gmofishsauce/yarc/img/2022-04-03/Clock and Downloader Extension Sketch.png

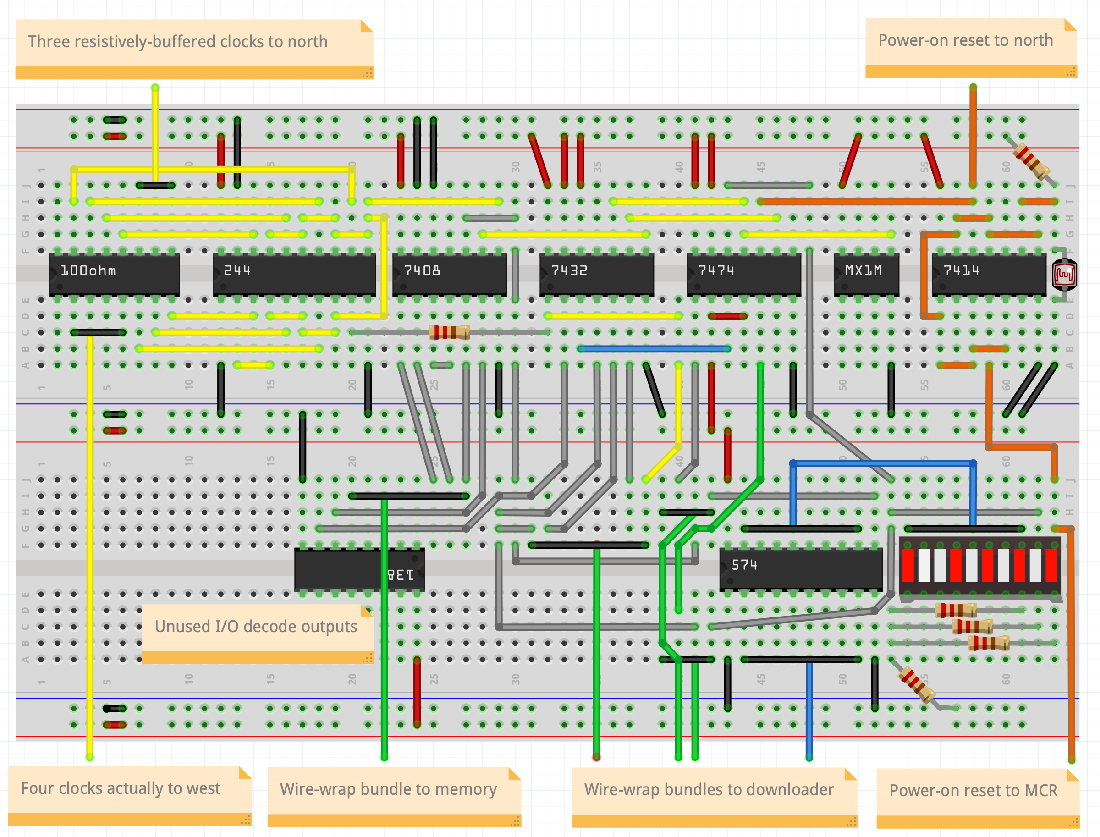
img/2022-04-03/Clock and Downloader Extension Sketch.png
