gmofishsauce/yarc/img/2022-04-03/Downloader Sketch.png

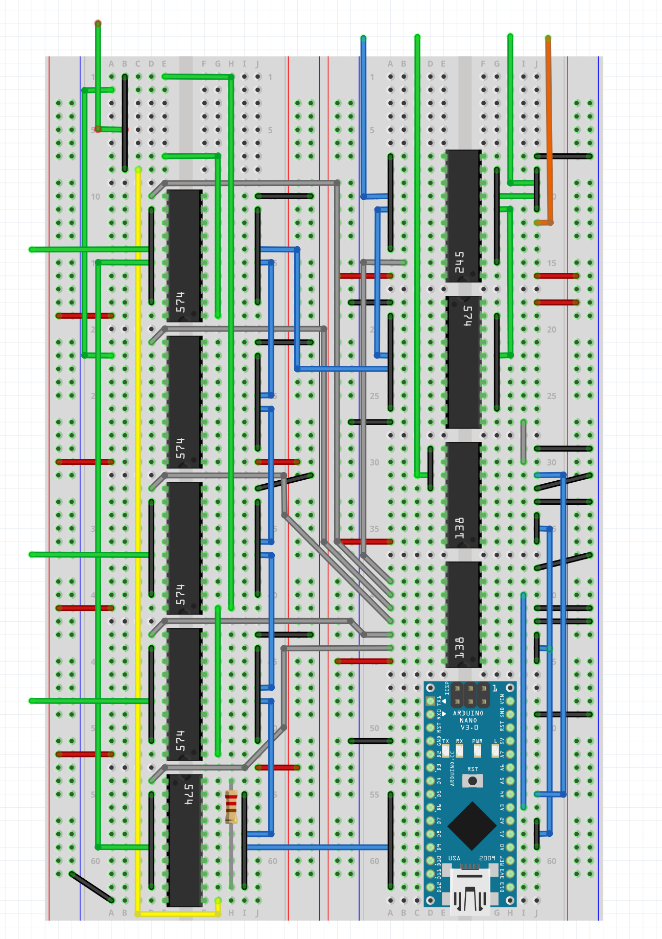
img/2022-04-03/Downloader Sketch.png
