gmofishsauce/yarc/img/2022-04-03/Memory Sketch (no busses).png

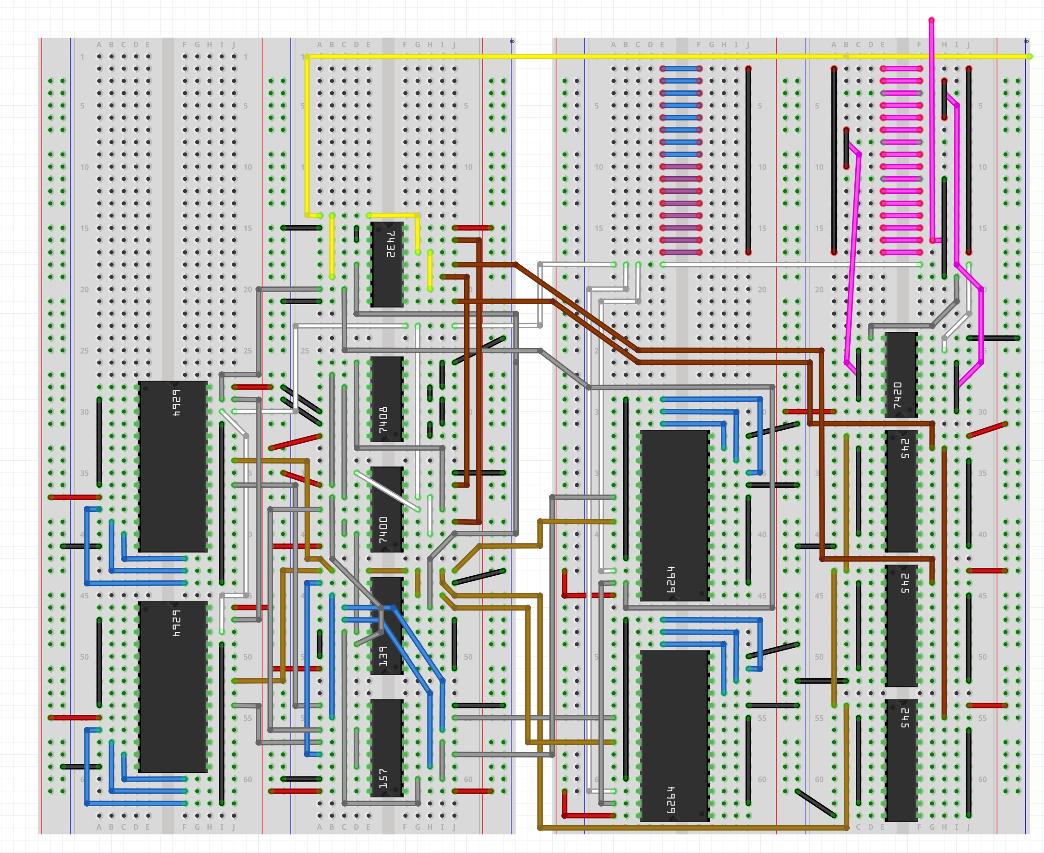
img/2022-04-03/Memory Sketch (no busses).png
