gmofishsauce/yarc/img/2022-07-07/clock_downloader_extension_fritzing.png

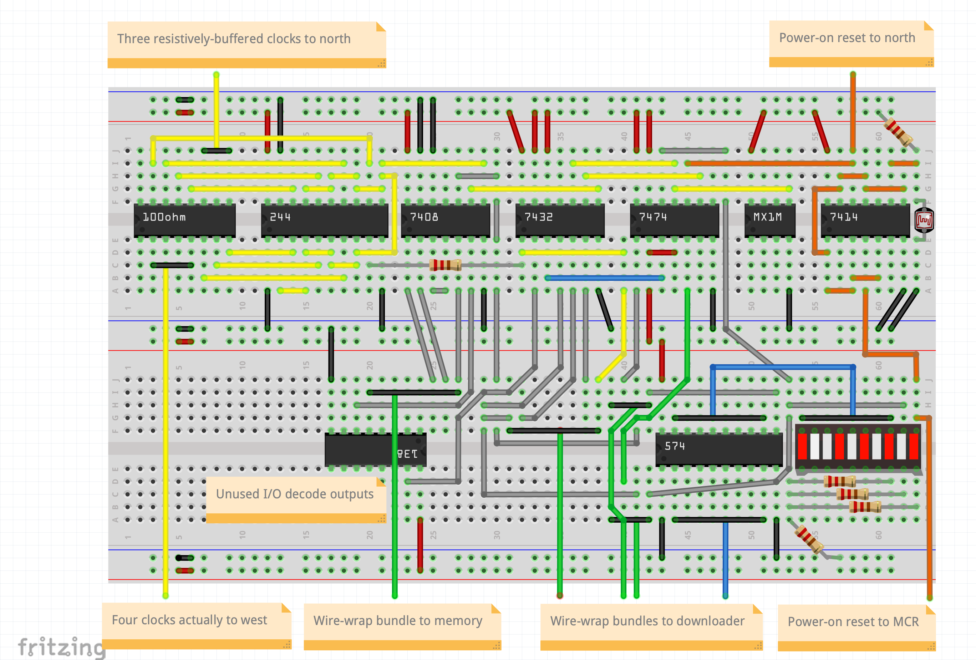
img/2022-07-07/clock_downloader_extension_fritzing.png
