gmofishsauce/yarc/img/2022-07-07/downloader_core_kicad.png

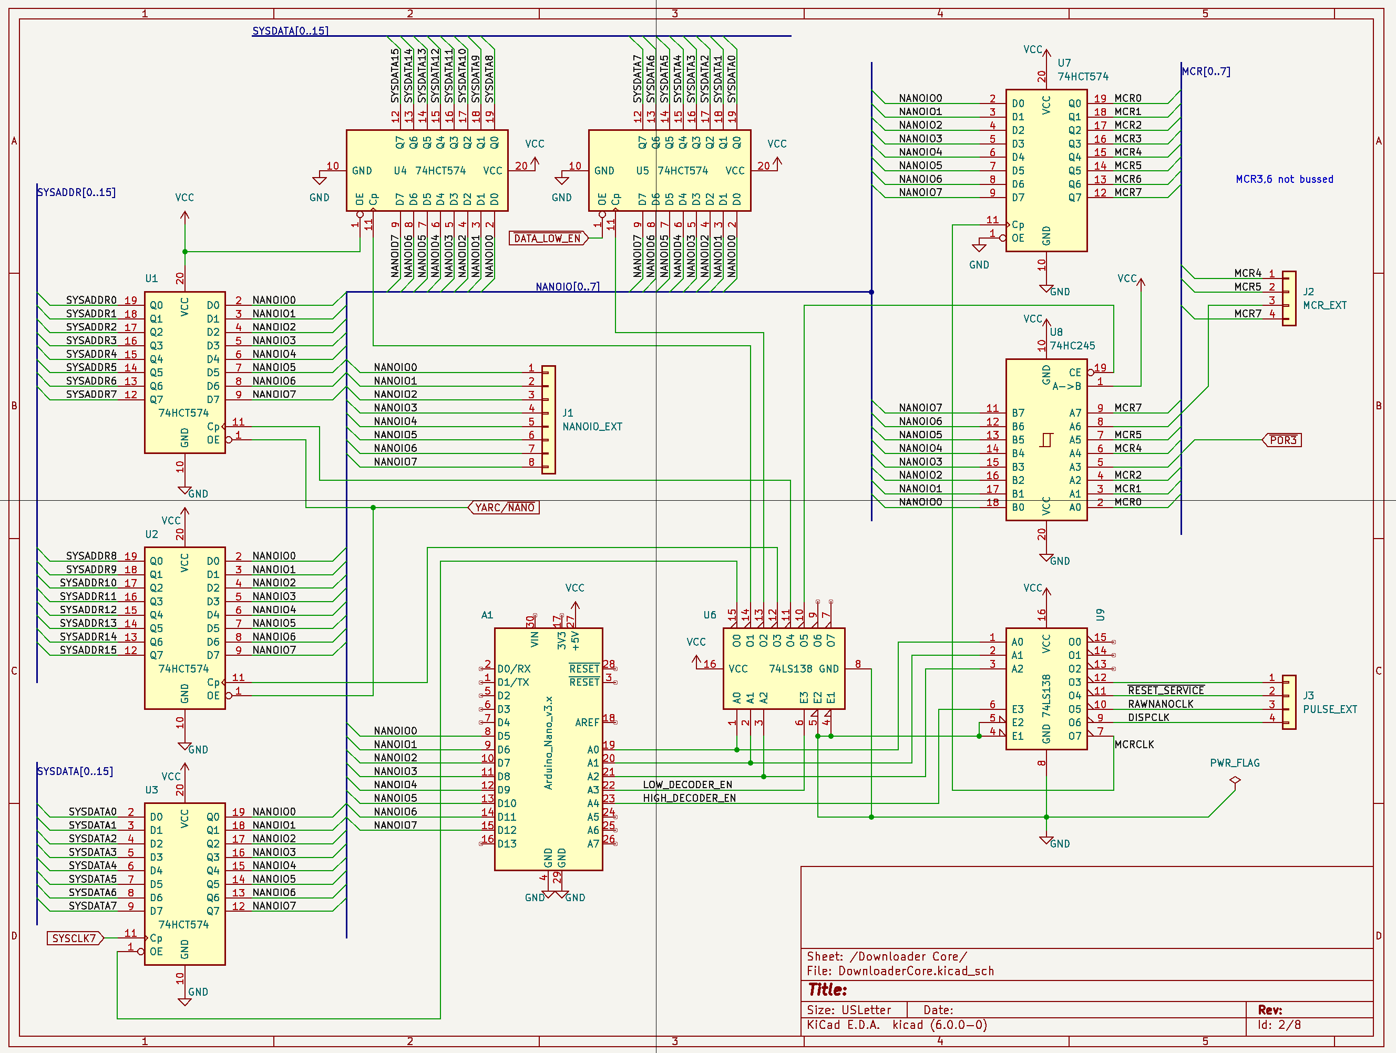
img/2022-07-07/downloader_core_kicad.png
