gmofishsauce/yarc/img/2022-07-07/downloader_fritzing.png

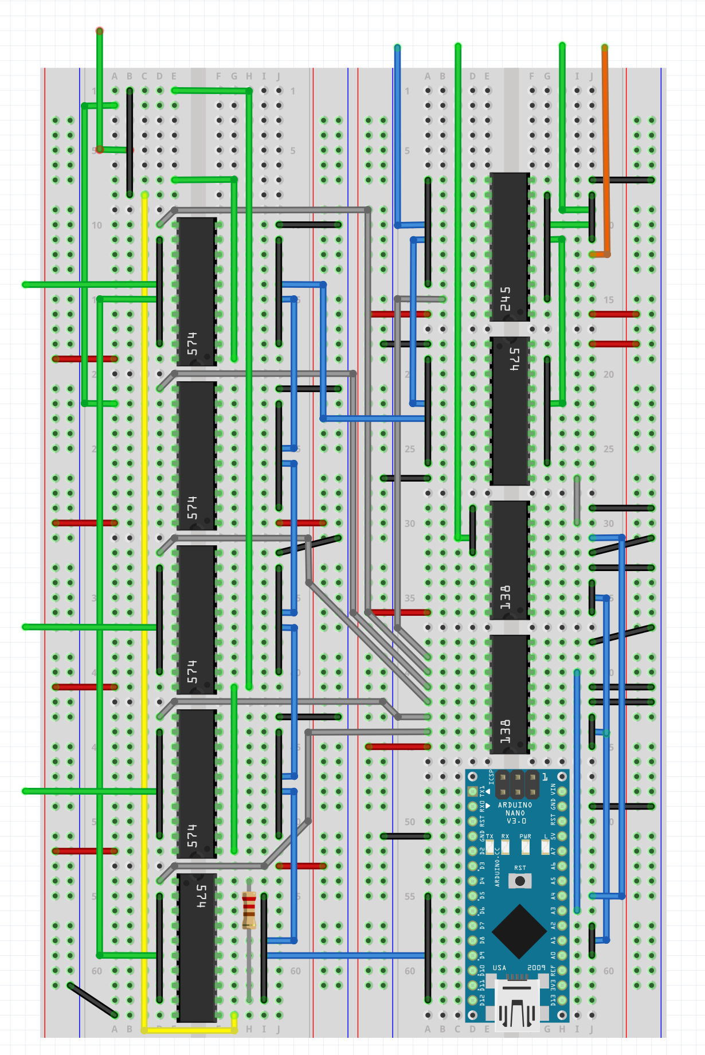
img/2022-07-07/downloader_fritzing.png
