gmofishsauce/yarc/img/2022-07-07/mem_pic_2.jpeg

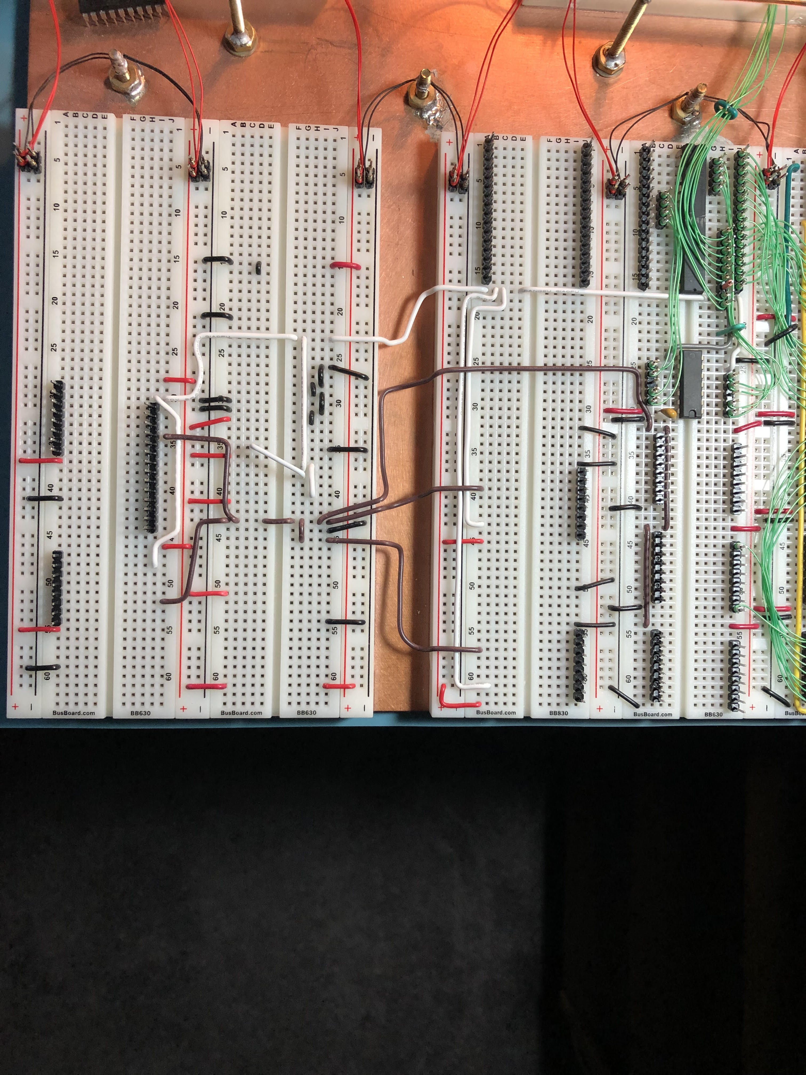
img/2022-07-07/mem_pic_2.jpeg
