gmofishsauce/yarc/img/2022-07-07/mem_pic_3.jpeg

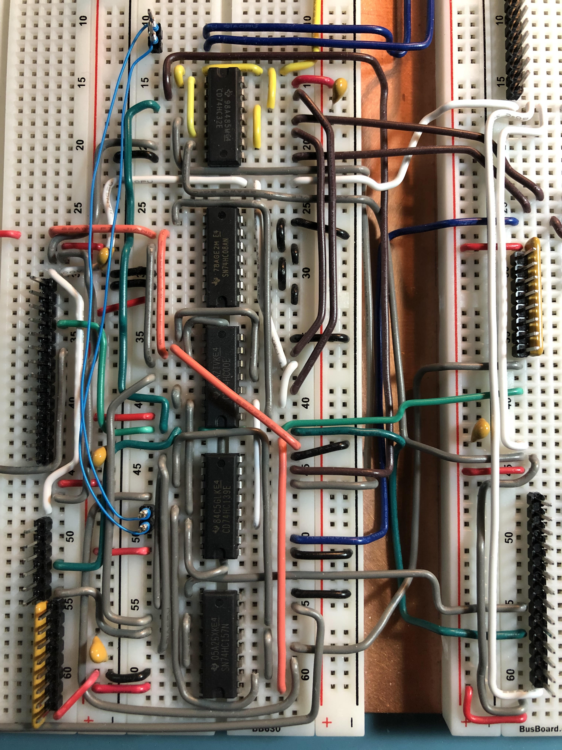
img/2022-07-07/mem_pic_3.jpeg
