gmofishsauce/yarc/img/2022-07-07/mem_pic_5.jpeg

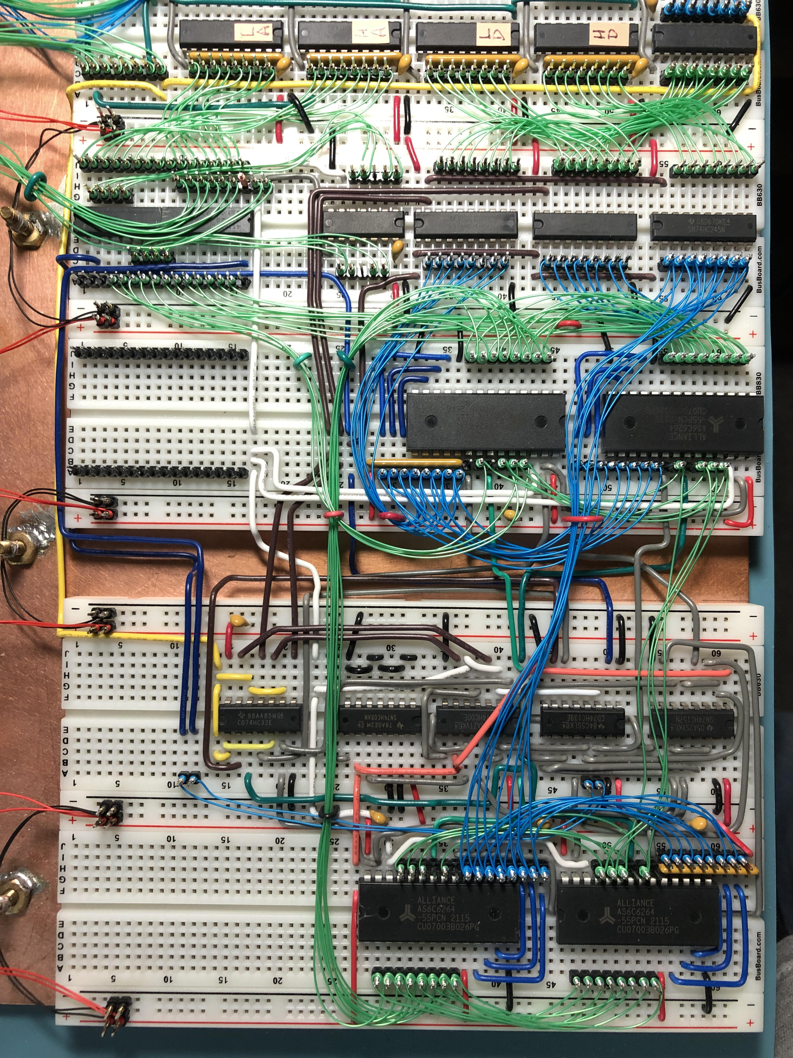
img/2022-07-07/mem_pic_5.jpeg
