gmofishsauce/yarc/img/2022-07-07/memory_fritzing.png

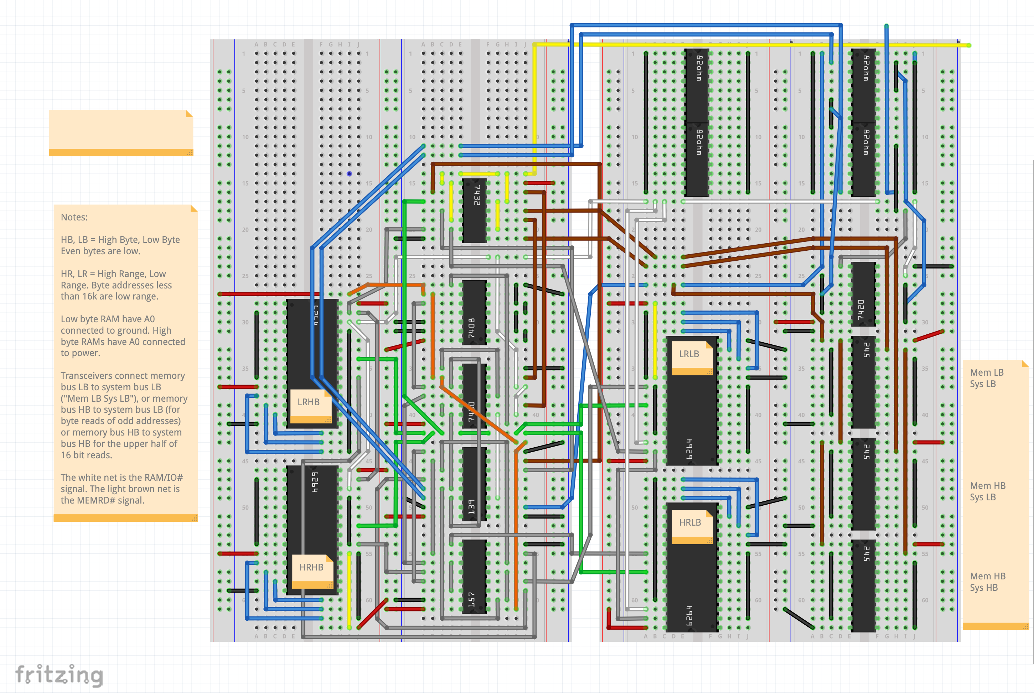
img/2022-07-07/memory_fritzing.png
