gmofishsauce/yarc/img/2022-07-07/memory_kicad.png

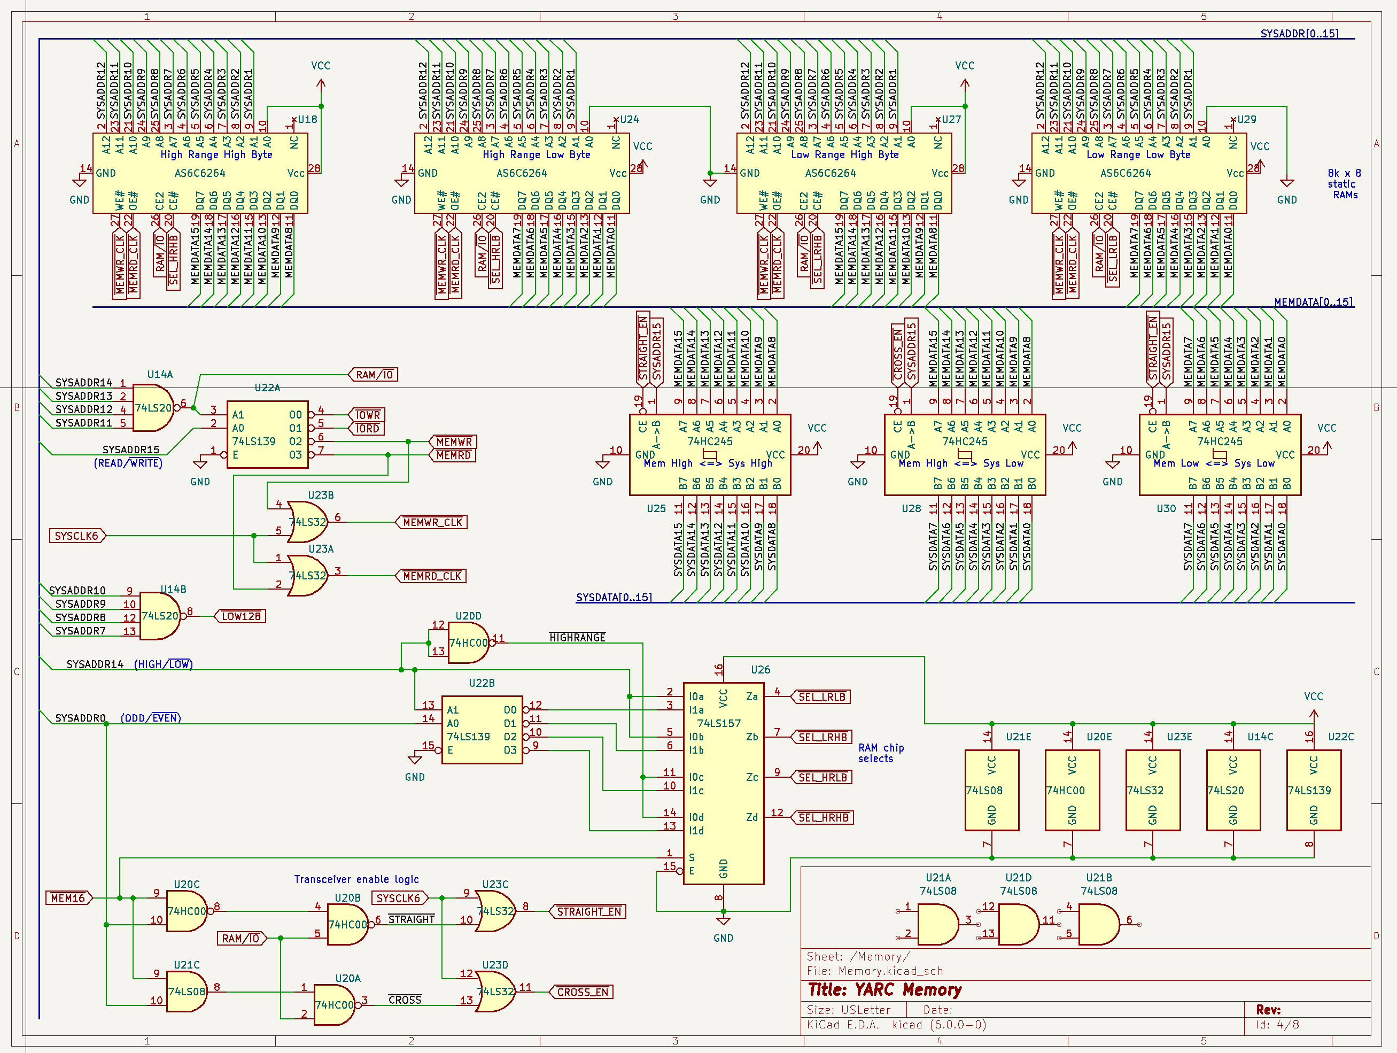
img/2022-07-07/memory_kicad.png
