gmofishsauce/yarc/img/2022-07-07/microcode_control_kicad.png

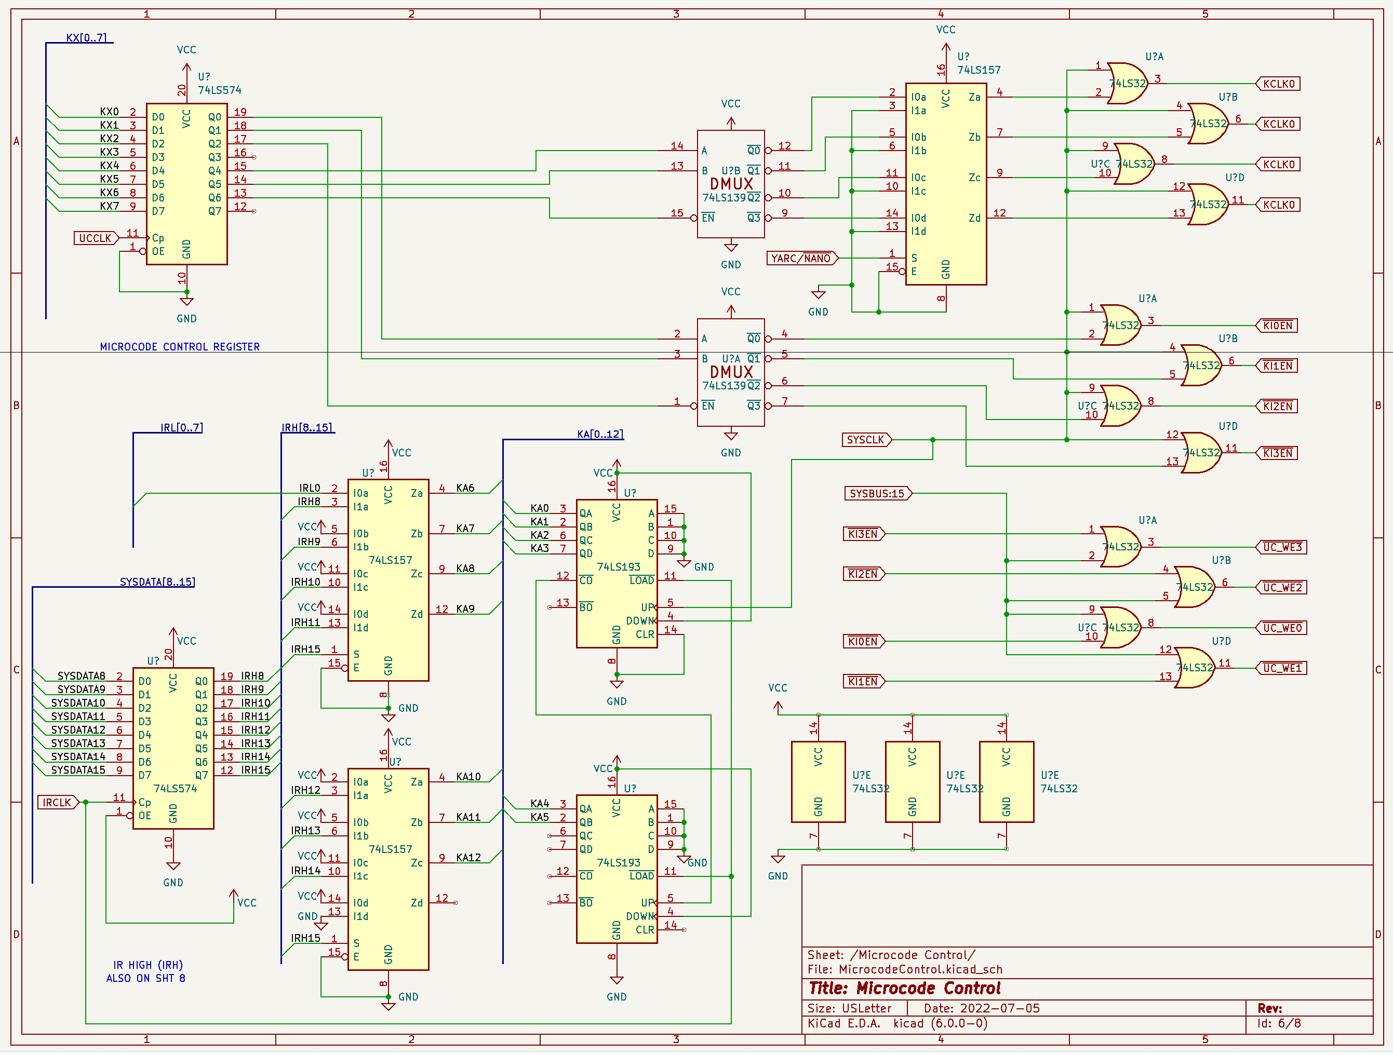
img/2022-07-07/microcode_control_kicad.png
