gmofishsauce/yarc/img/2022-07-07/microcode_fritzing.png

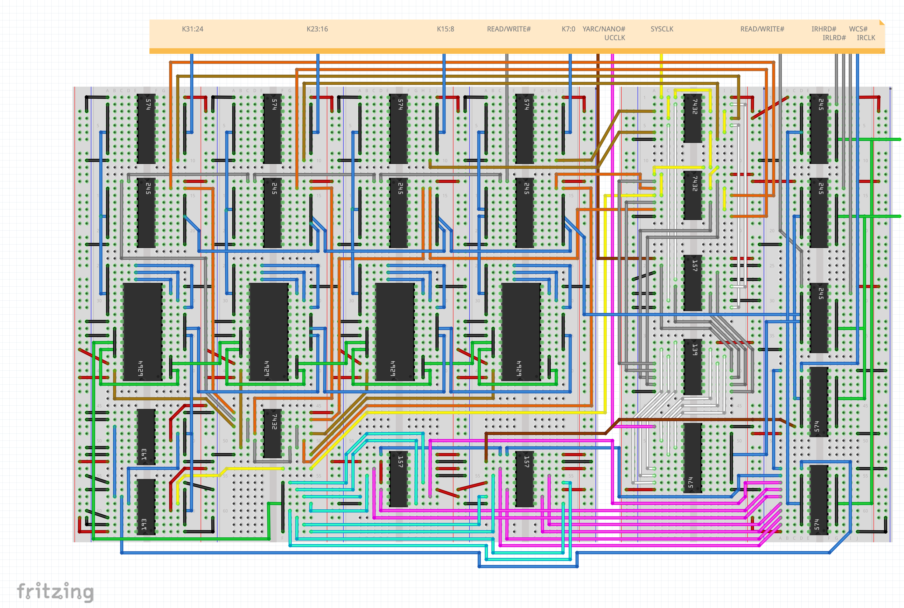
img/2022-07-07/microcode_fritzing.png
