gmofishsauce/yarc/img/2022-07-07/microcode_transceivers_kicad.png

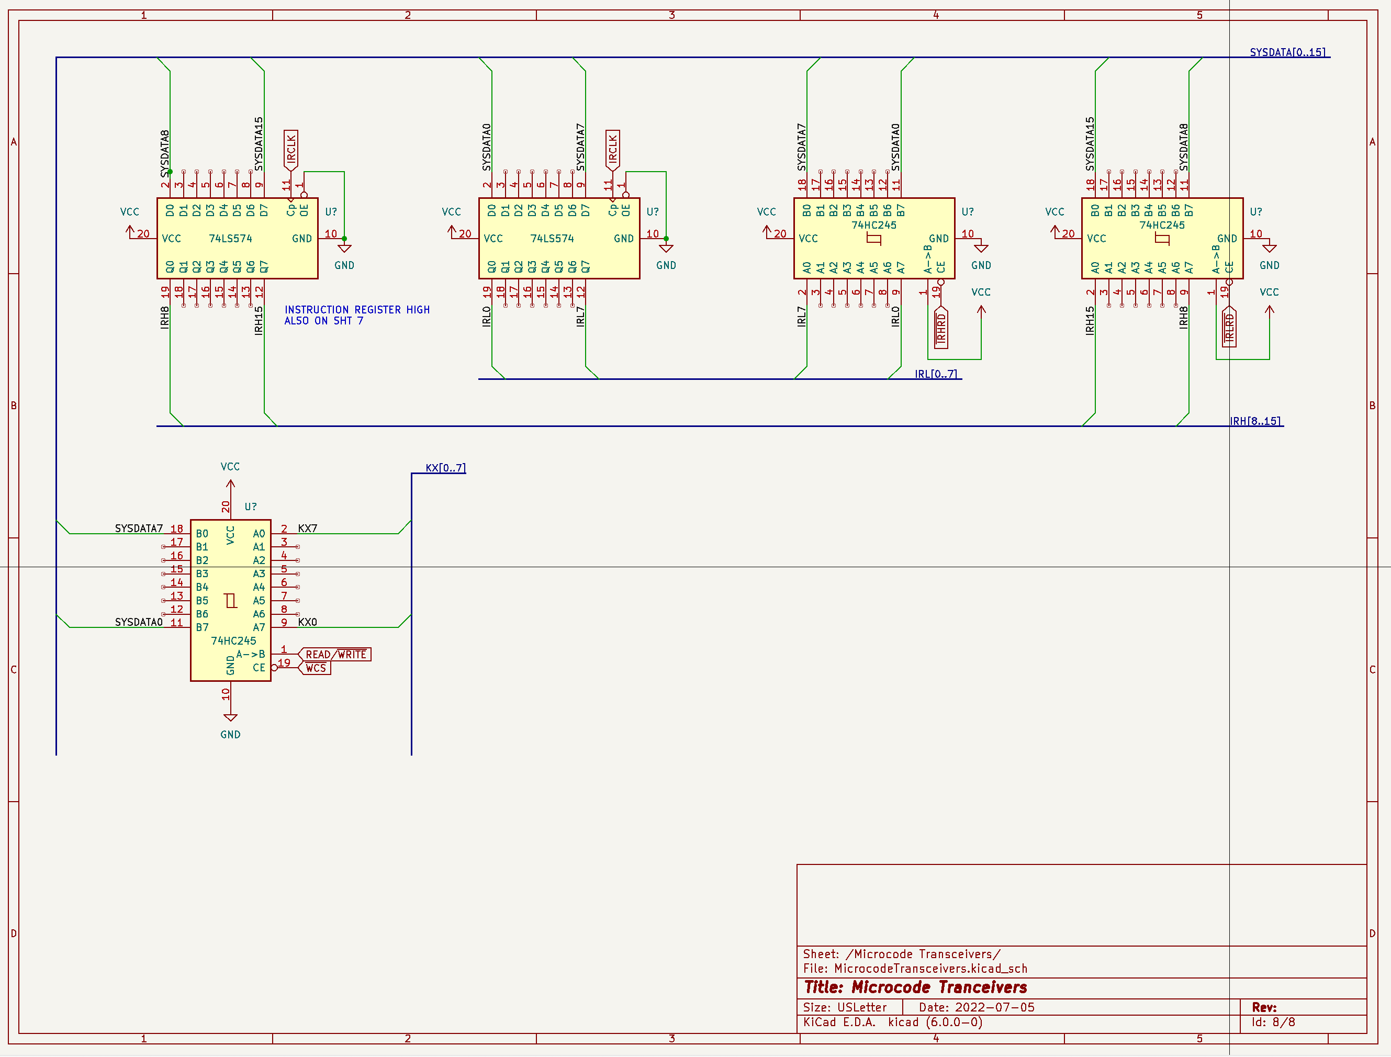
img/2022-07-07/microcode_transceivers_kicad.png
