gmofishsauce/yarc/img/2022-07-07/microode_engine_kicad.png

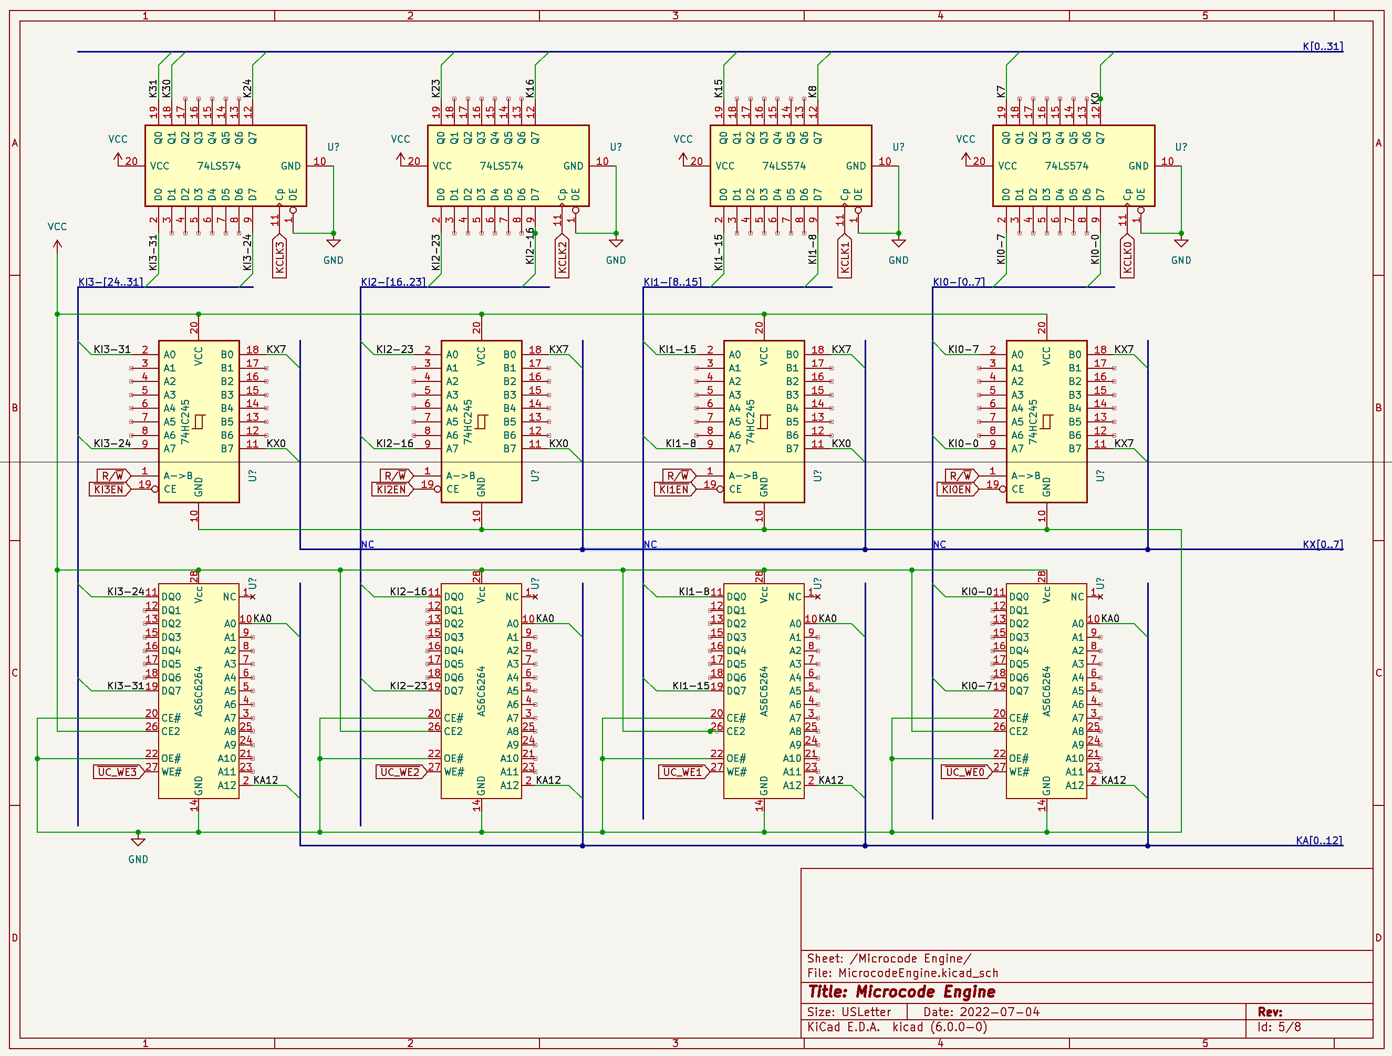
img/2022-07-07/microode_engine_kicad.png
