gmofishsauce/yarc/img/2022-07-07/Packaging-1.jpg

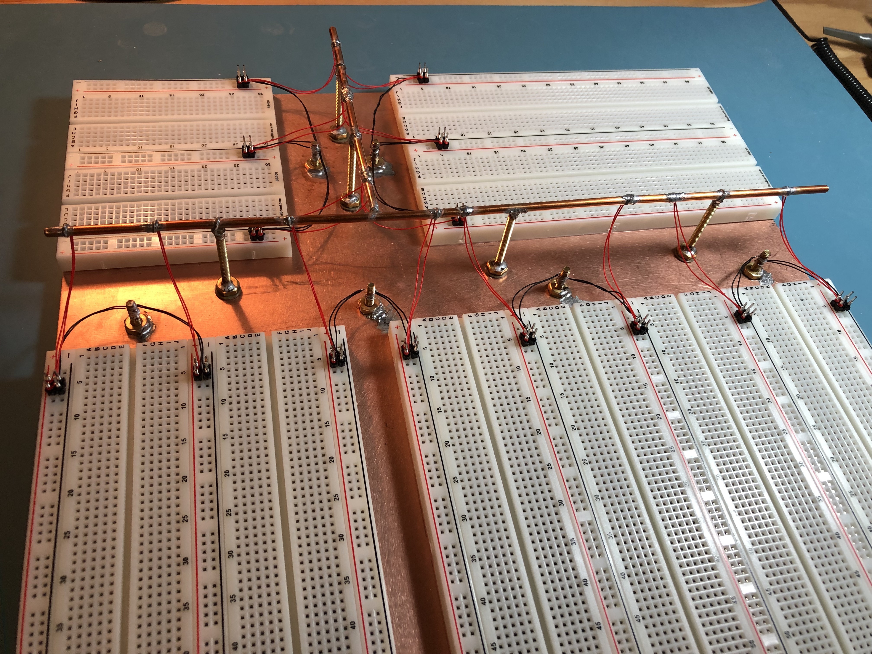
img/2022-07-07/Packaging-1.jpg
