gmofishsauce/yarc/img/2022-07-07/Packaging-2.jpg

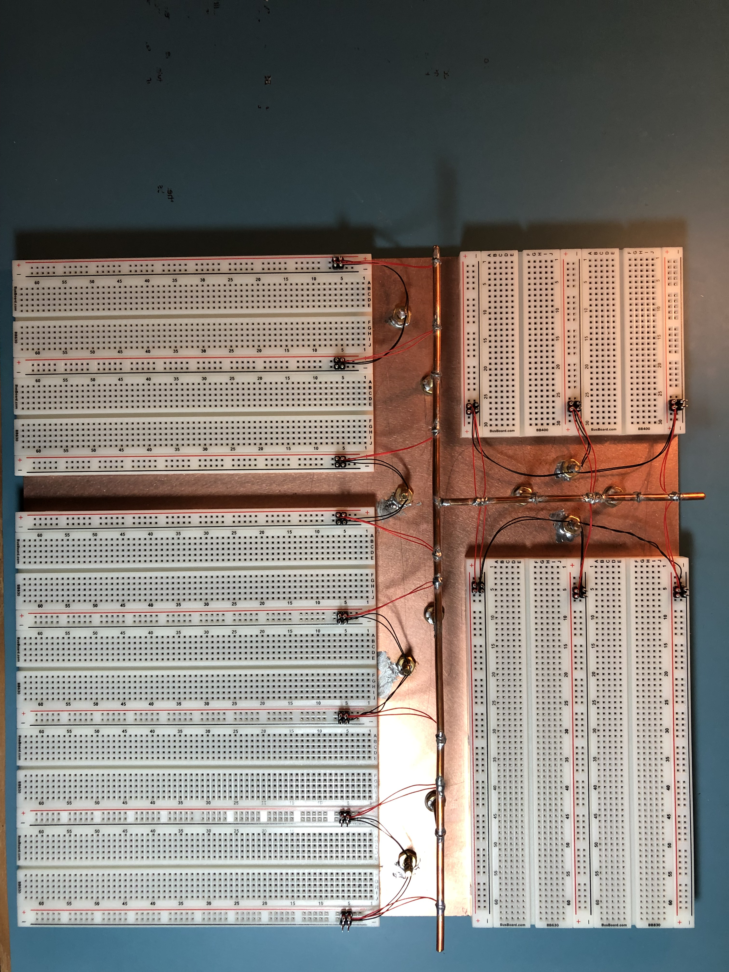
img/2022-07-07/Packaging-2.jpg
