gmofishsauce/yarc/img/2022-07-07/root_kicad.png

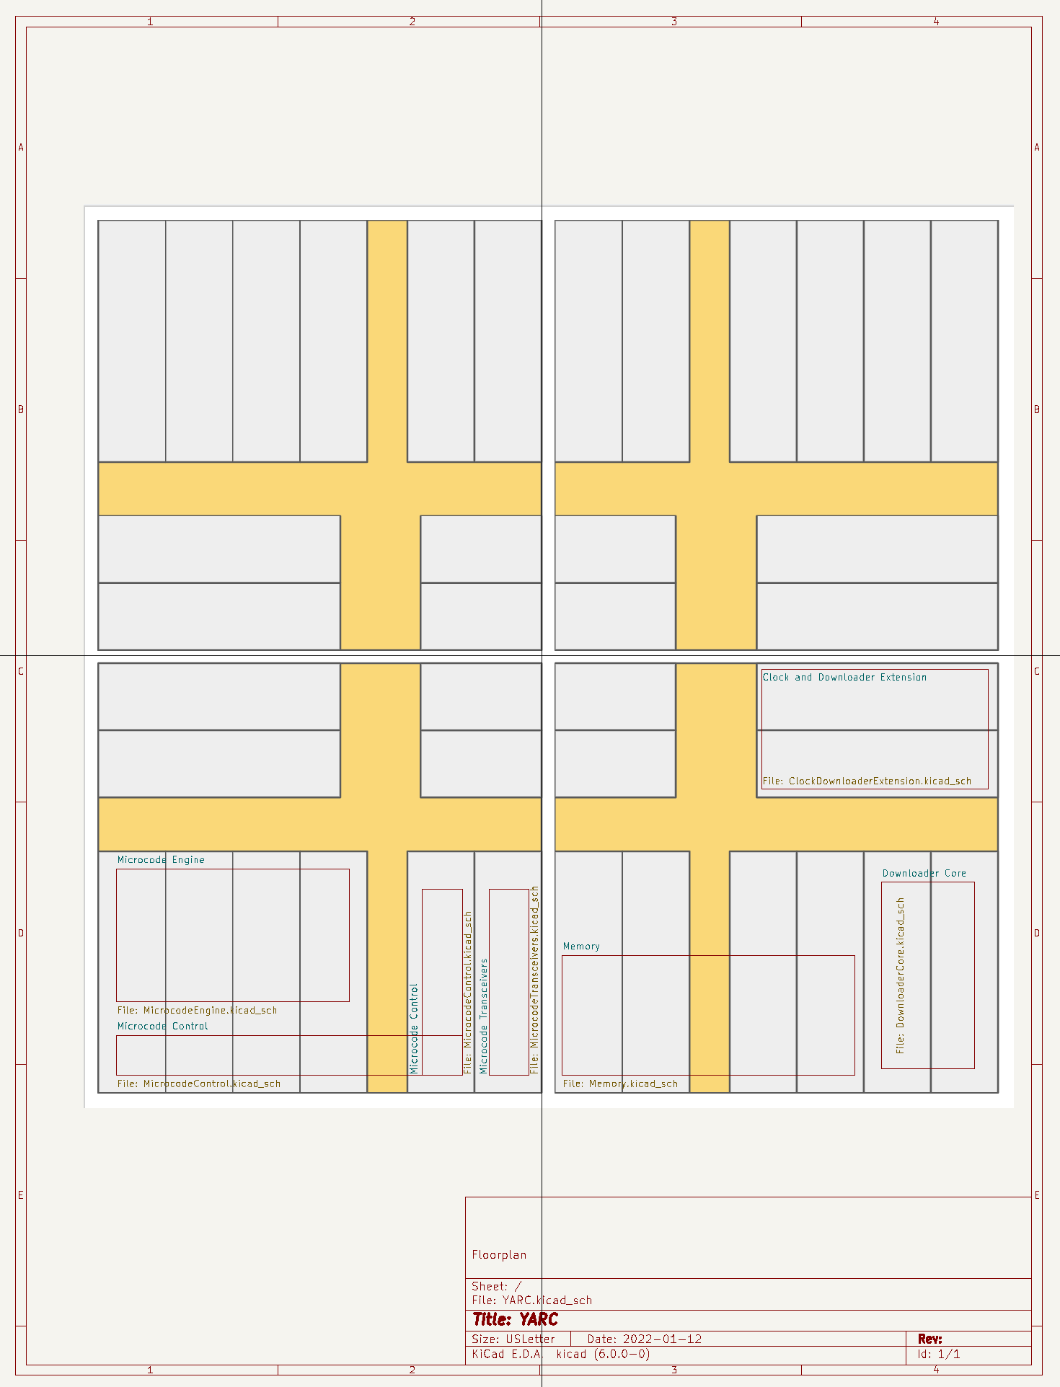
img/2022-07-07/root_kicad.png
