gmofishsauce/yarc/img/2022-10-18/ALU.png

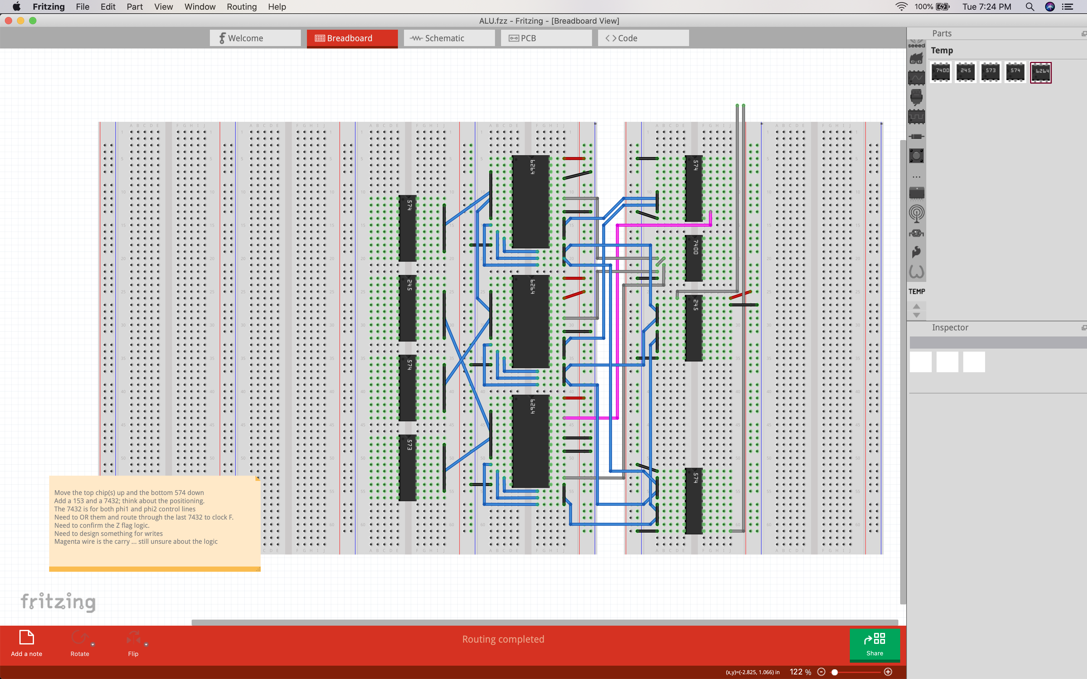
img/2022-10-18/ALU.png
