gmofishsauce/yarc/img/2022-10-18/Central.png

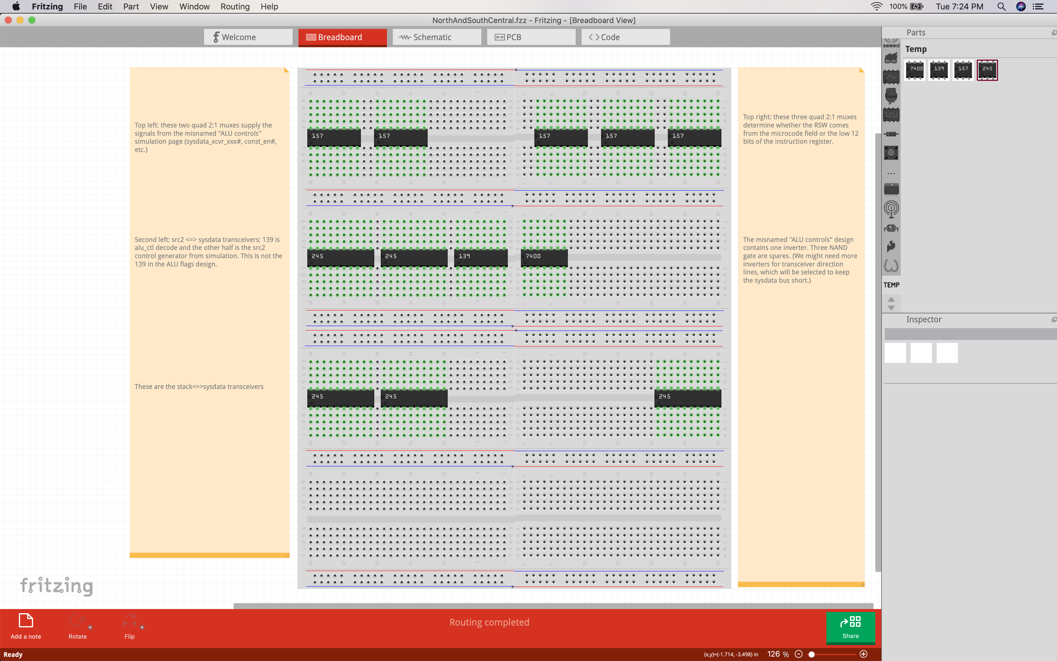
img/2022-10-18/Central.png
