gmofishsauce/yarc/img/2022-10-18/Clock.png

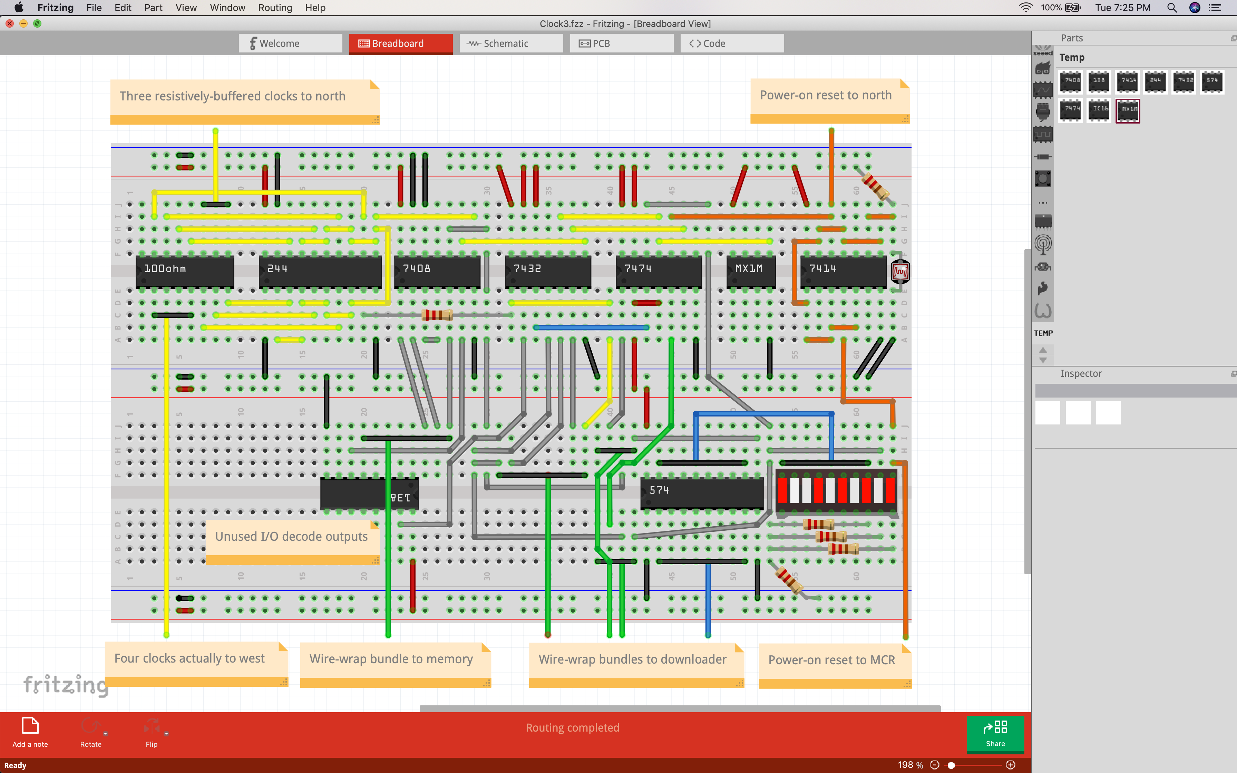
img/2022-10-18/Clock.png
