gmofishsauce/yarc/img/2022-10-18/Flags.png

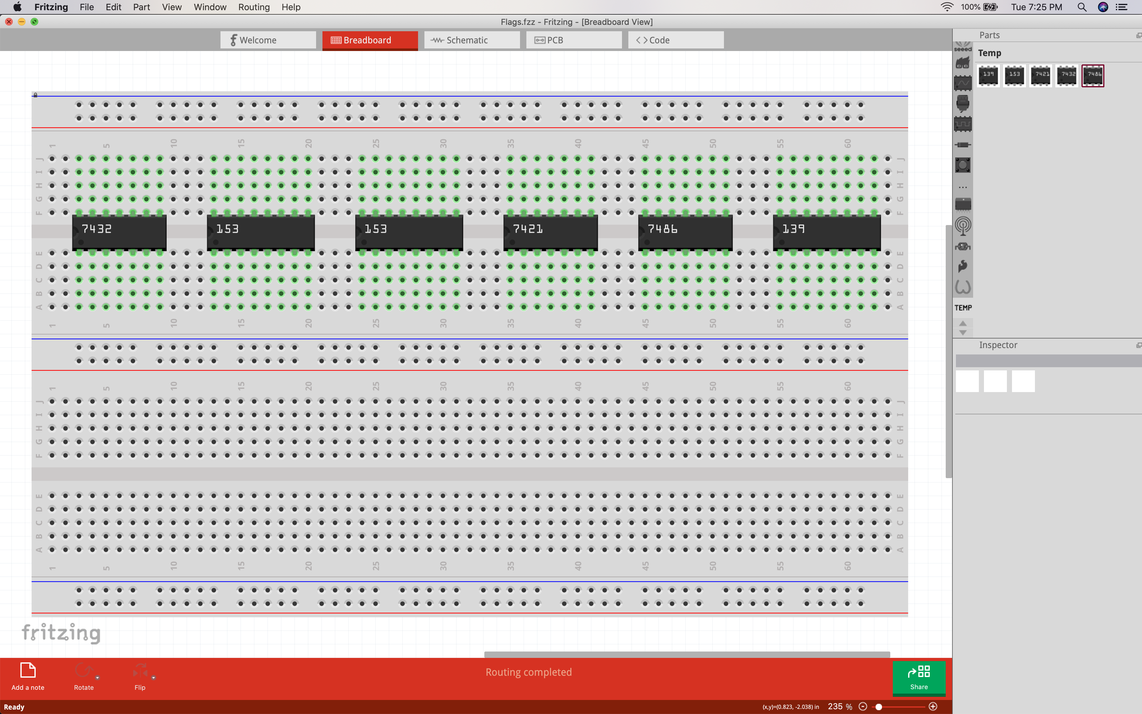
img/2022-10-18/Flags.png
