gmofishsauce/yarc/img/2022-10-18/Microcode.png

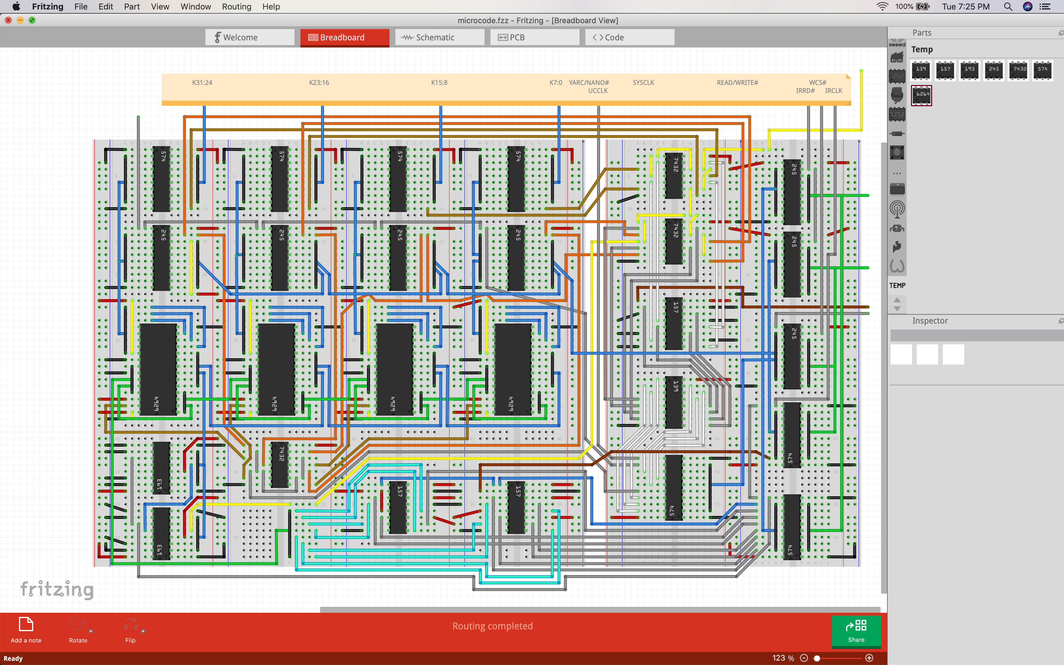
img/2022-10-18/Microcode.png
