gmofishsauce/yarc/img/2022-10-18/RAM-busses.png

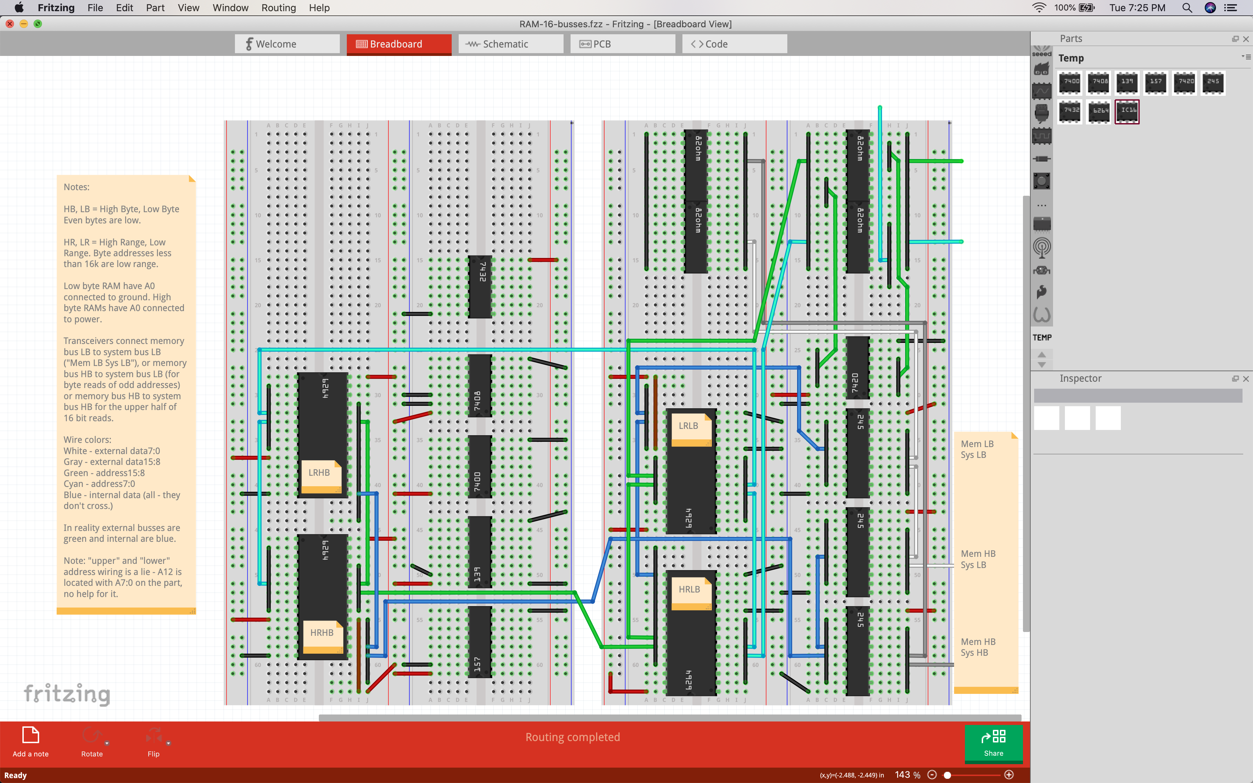
img/2022-10-18/RAM-busses.png
