gmofishsauce/yarc/img/2022-10-18/RAM-logic.png

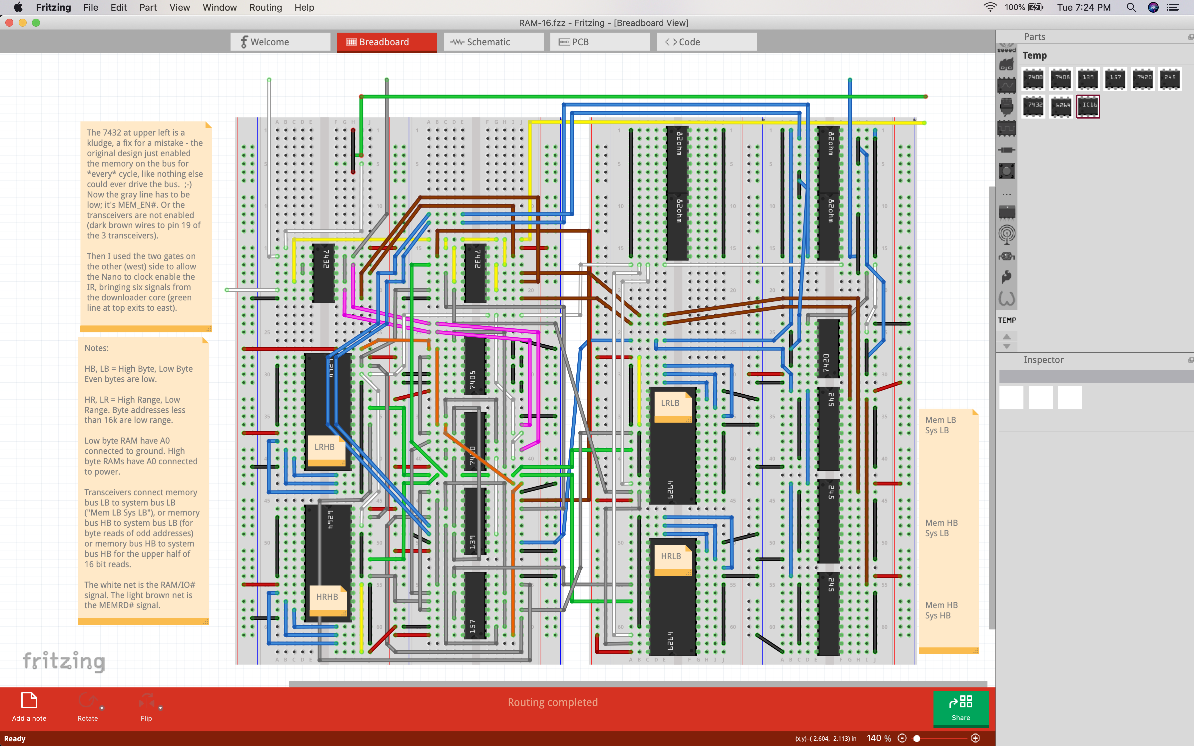
img/2022-10-18/RAM-logic.png
