gmofishsauce/yarc/img/2022-10-18/Registers.png

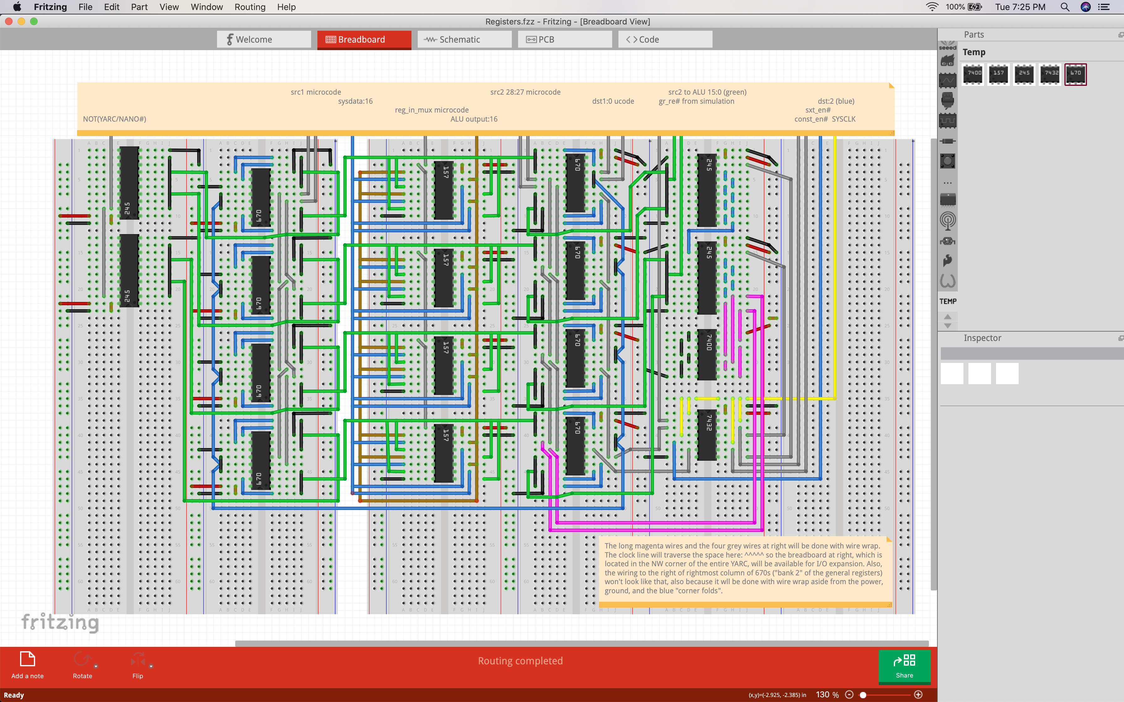
img/2022-10-18/Registers.png
