gmofishsauce/yarc/img/2022-10-18/Stacks.png

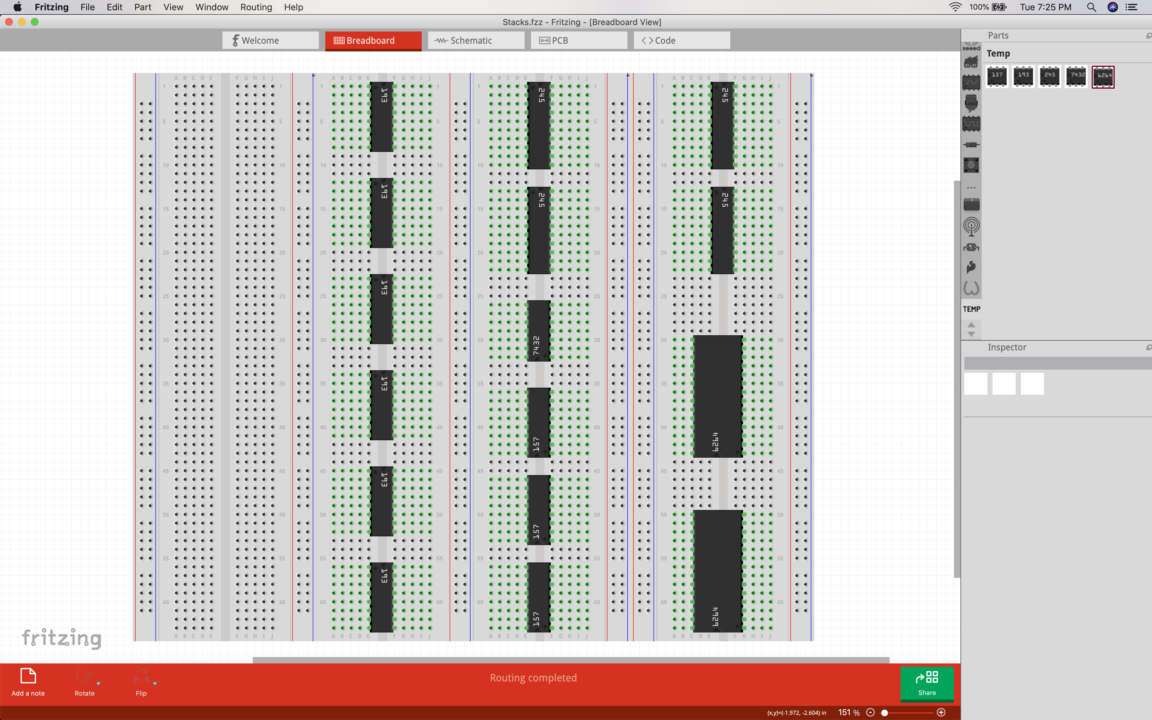
img/2022-10-18/Stacks.png
