gmofishsauce/yarc/img/2022-11-16/CurrentStatusNov16.jpeg

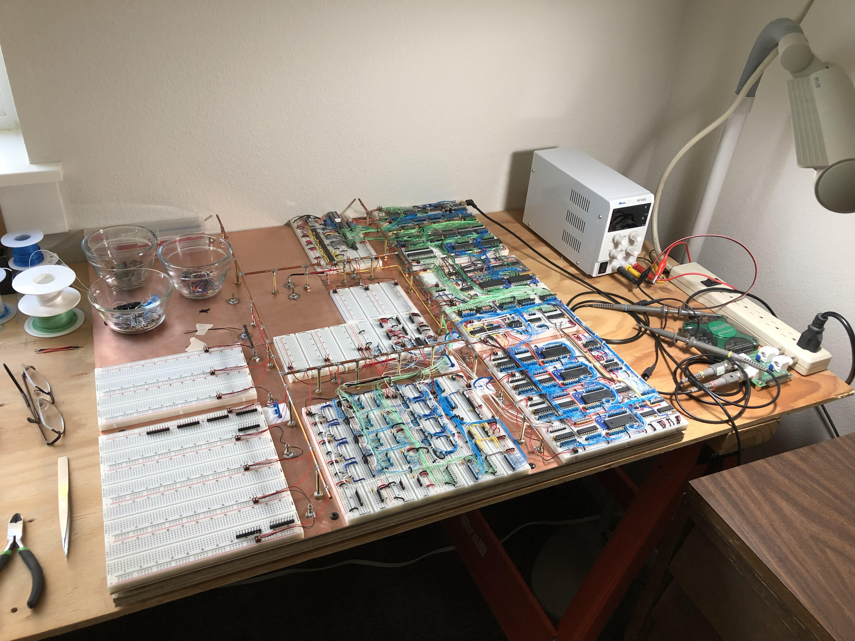
img/2022-11-16/CurrentStatusNov16.jpeg
