gmofishsauce/yarc/img/2022-11-16/Fritzing/ALU_bb.png

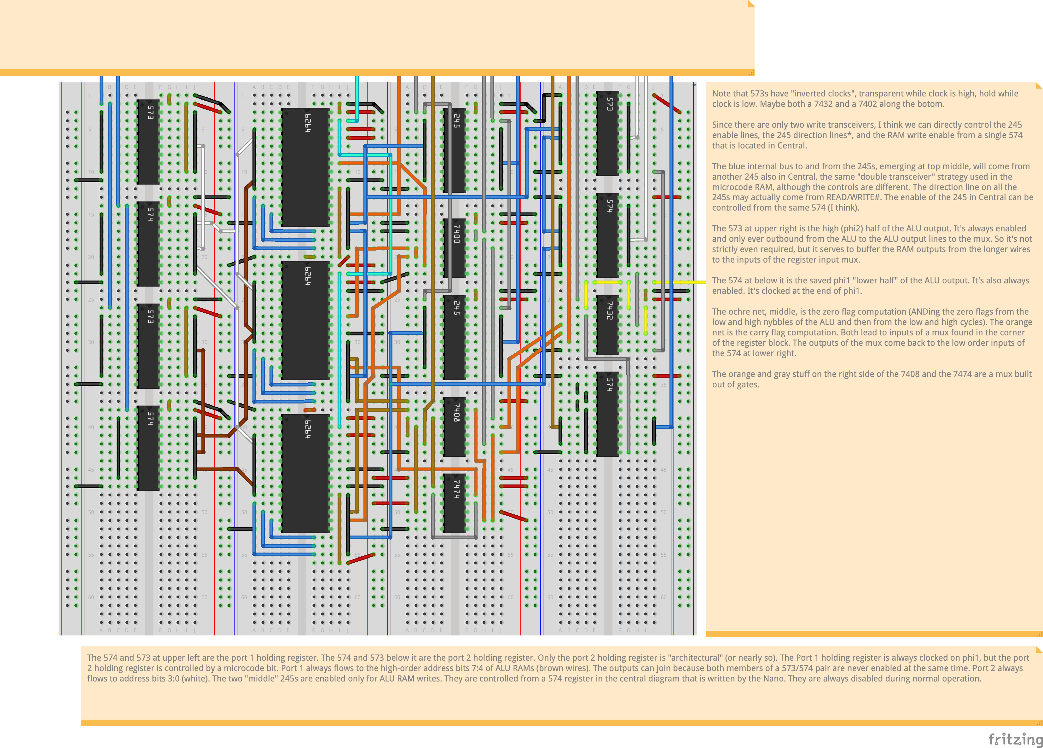
img/2022-11-16/Fritzing/ALU_bb.png
