gmofishsauce/yarc/img/2022-11-16/Fritzing/Clock3_bb.png

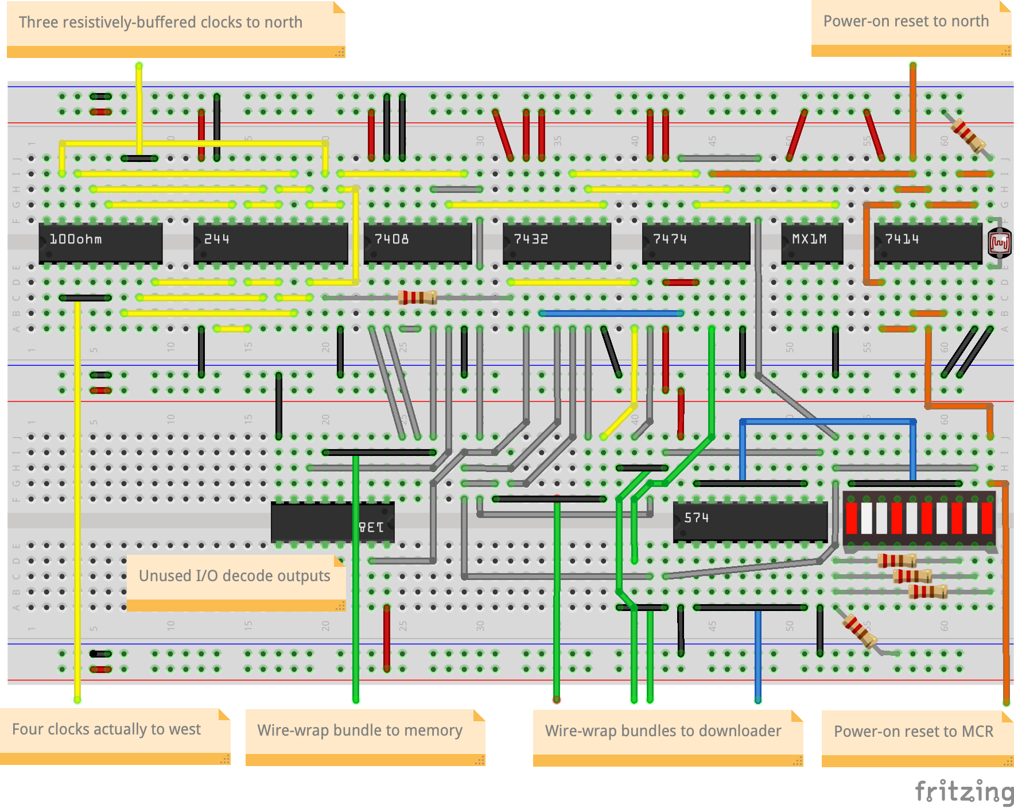
img/2022-11-16/Fritzing/Clock3_bb.png
