gmofishsauce/yarc/img/2022-11-16/Fritzing/Downloader_bb.png

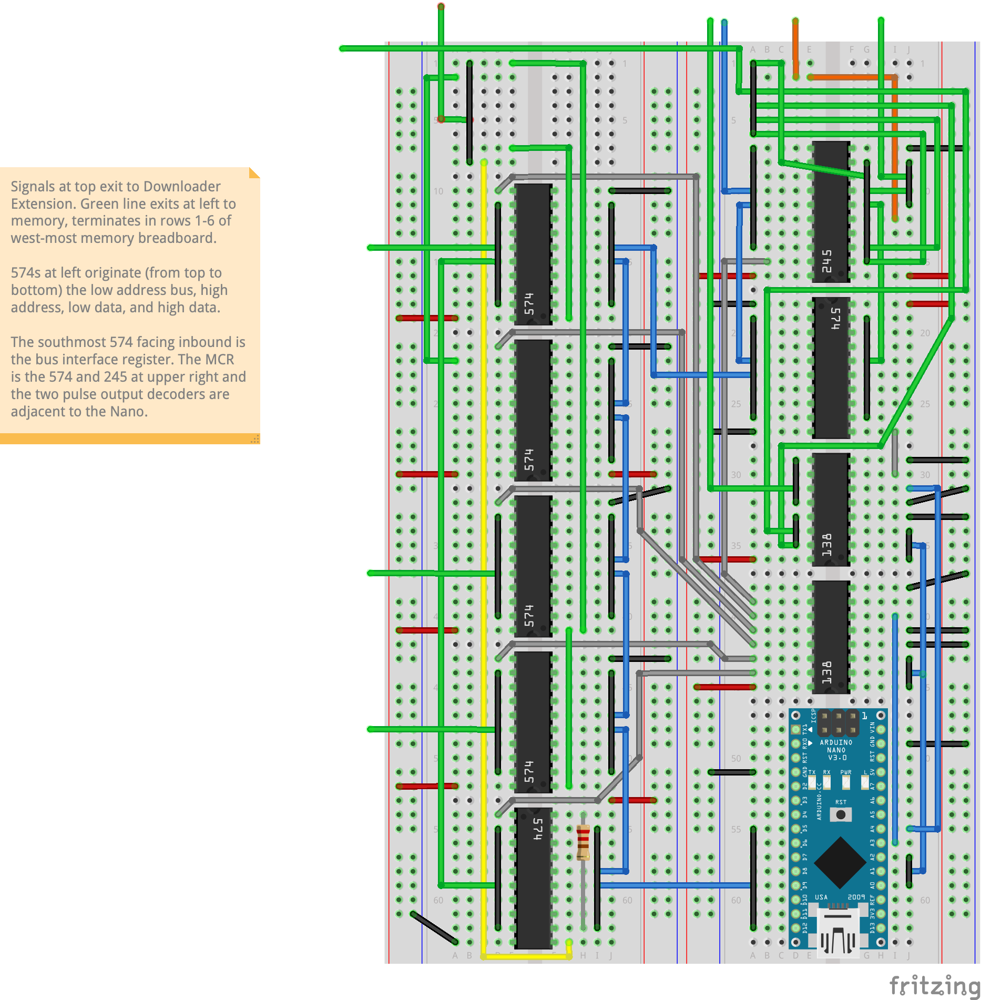
img/2022-11-16/Fritzing/Downloader_bb.png
