gmofishsauce/yarc/img/2022-11-16/Fritzing/microcode_bb.png

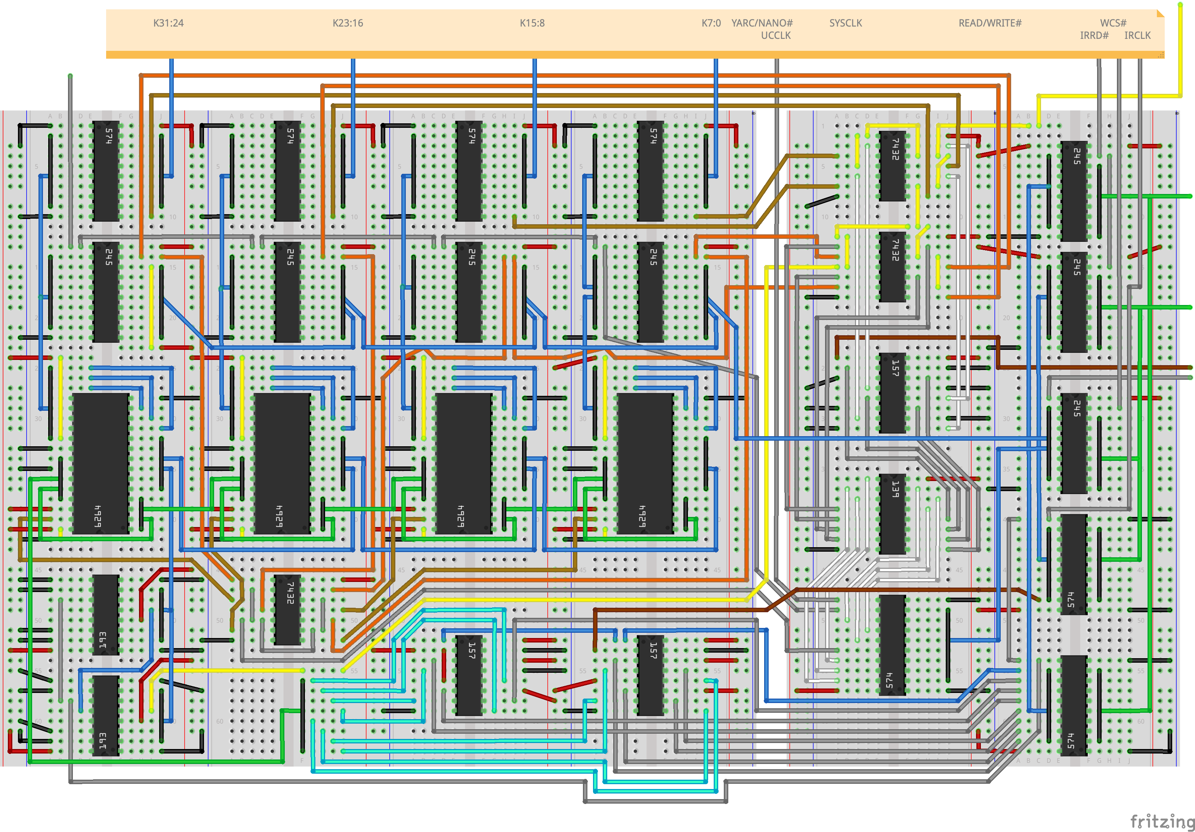
img/2022-11-16/Fritzing/microcode_bb.png
