gmofishsauce/yarc/img/2022-11-16/Fritzing/NorthAndSouthCentral_bb.png

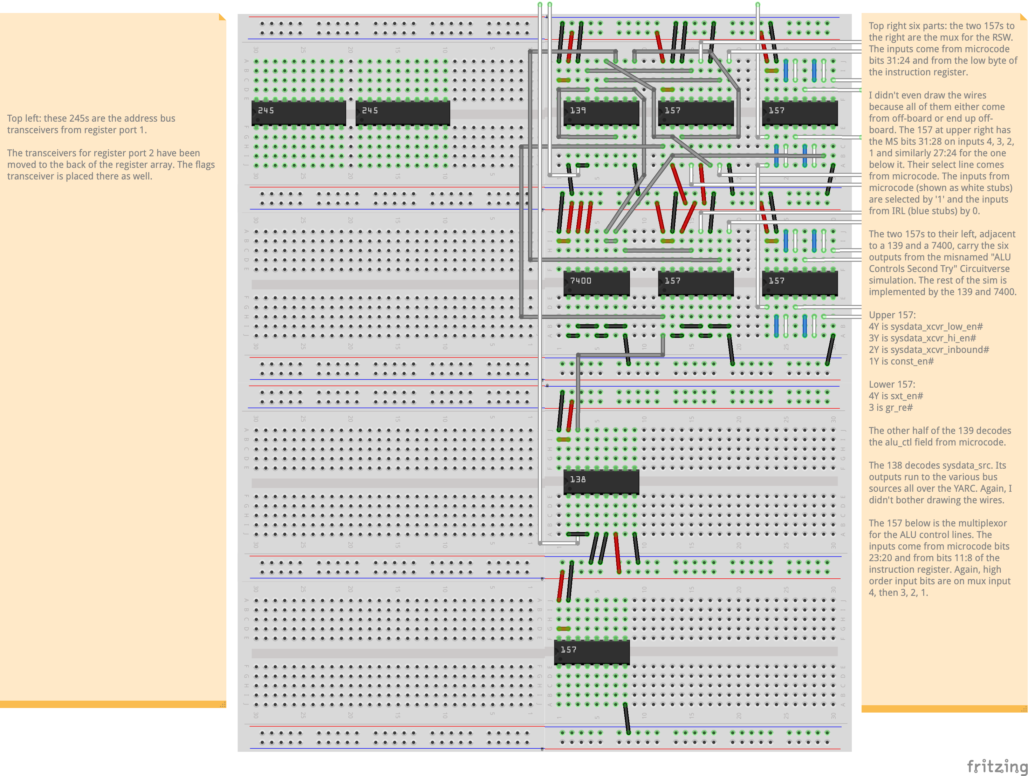
img/2022-11-16/Fritzing/NorthAndSouthCentral_bb.png
