gmofishsauce/yarc/img/2022-11-16/Fritzing/RAM-16_bb.png

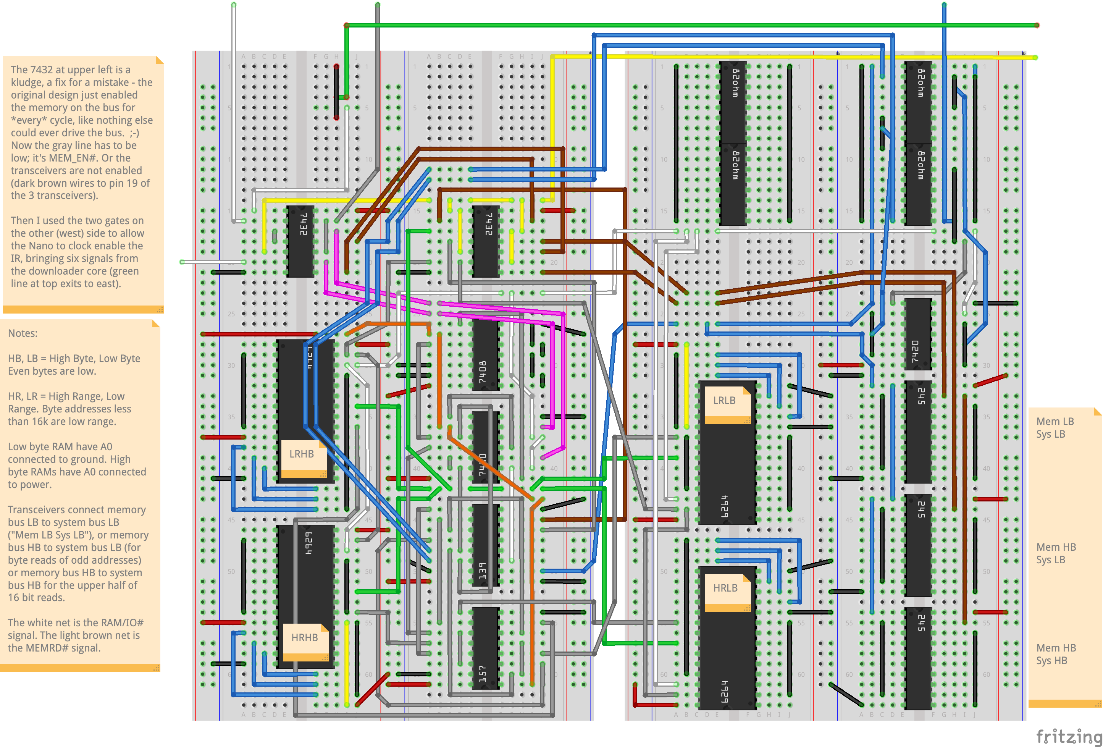
img/2022-11-16/Fritzing/RAM-16_bb.png
