gmofishsauce/yarc/img/2022-11-16/Fritzing/Registers_bb.png

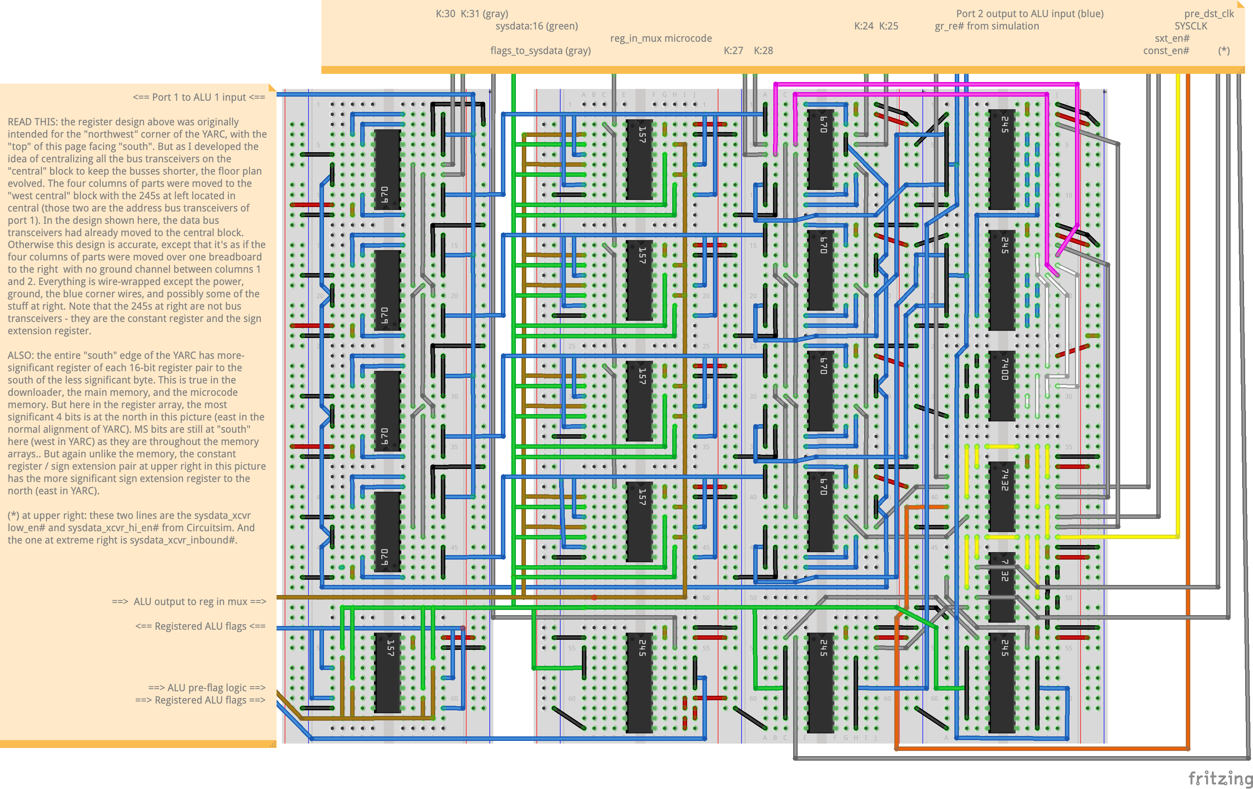
img/2022-11-16/Fritzing/Registers_bb.png
