gmofishsauce/yarc/img/2022-11-16/Fritzing/Stacks_bb.png

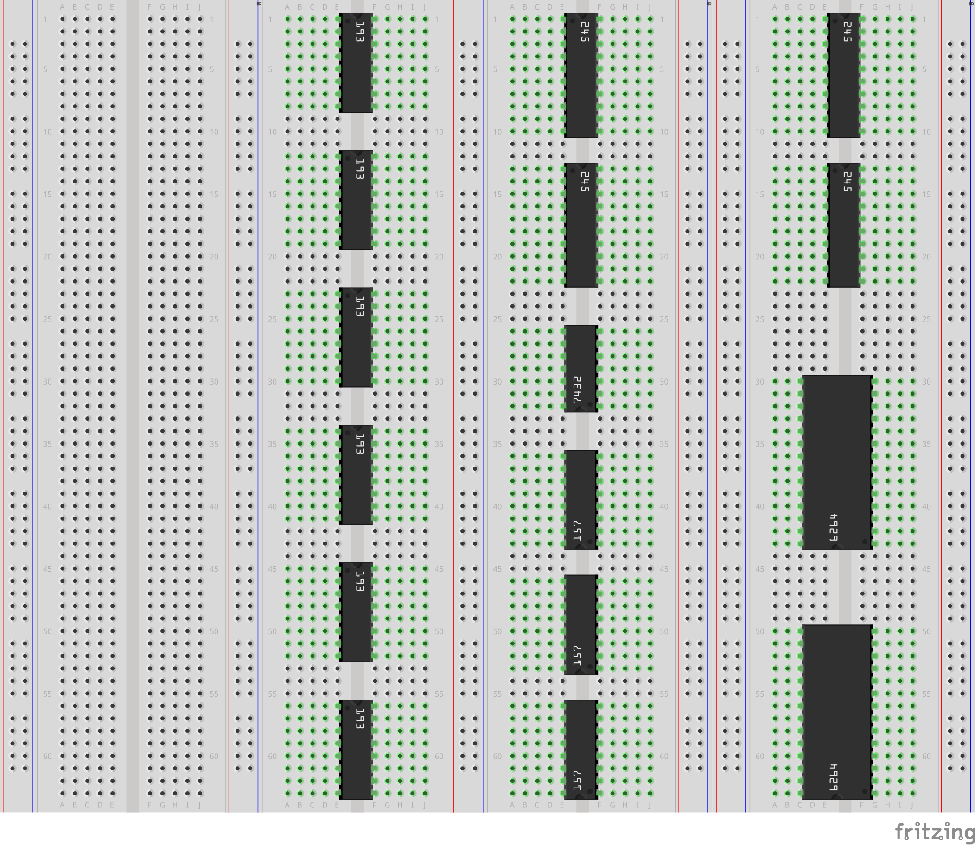
img/2022-11-16/Fritzing/Stacks_bb.png
