gmofishsauce/yarc/img/2023-06-20/IMG-0663.jpg

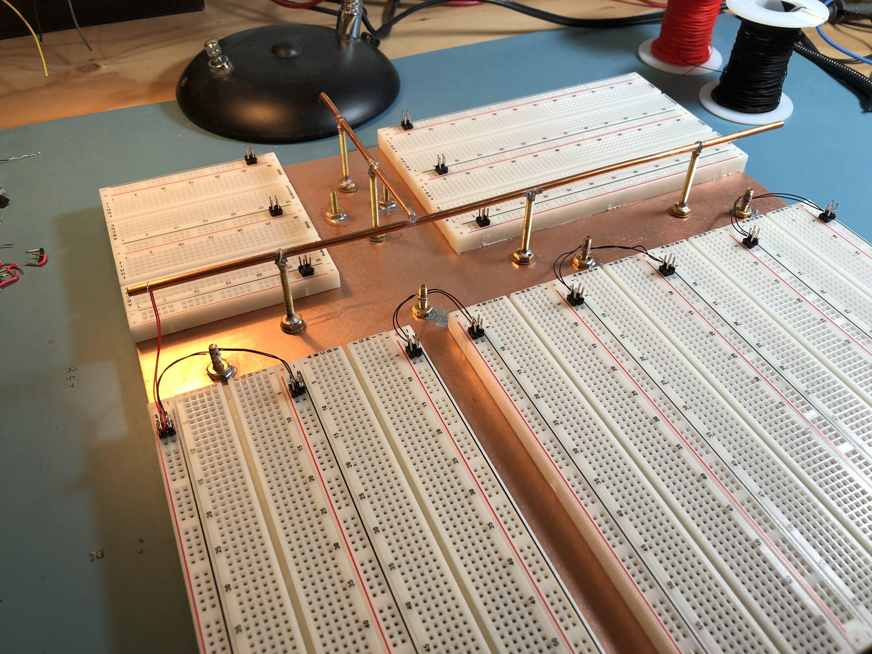
img/2023-06-20/IMG-0663.jpg
