gmofishsauce/yarc/img/2023-06-20/IMG-1106.jpg

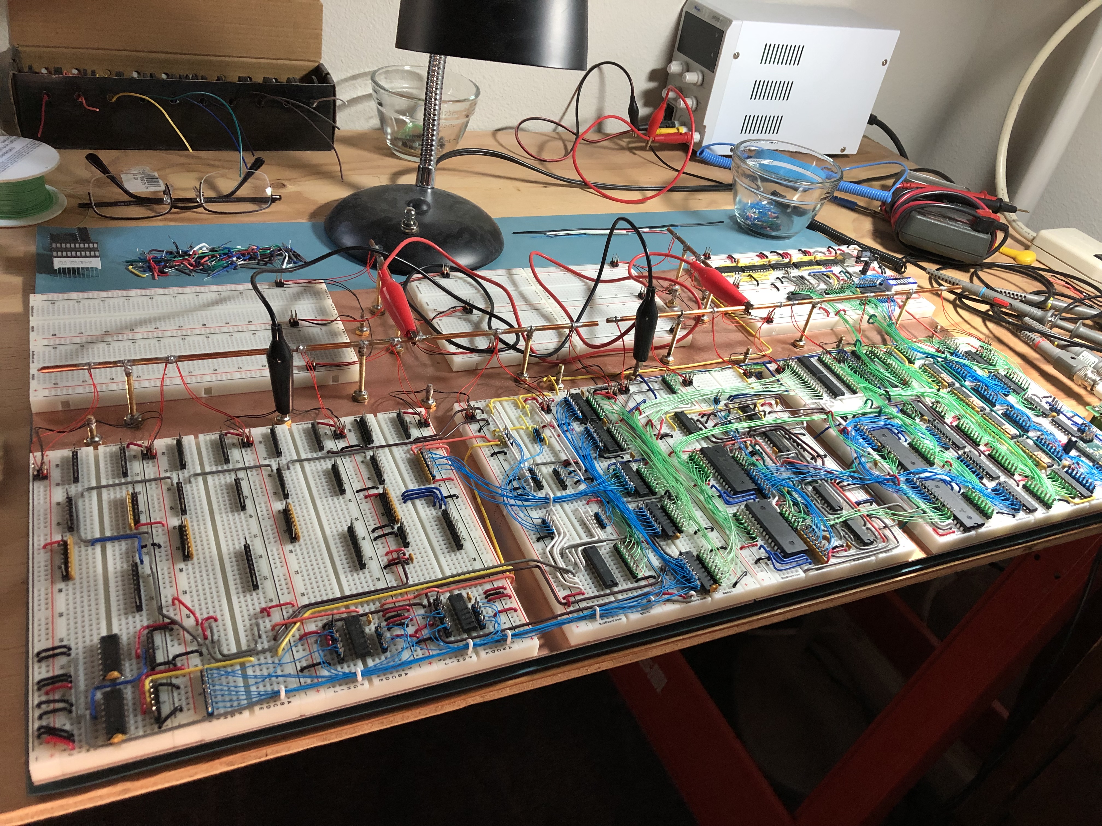
img/2023-06-20/IMG-1106.jpg
