gmofishsauce/yarc/img/2023-06-20/IMG-1128.jpg

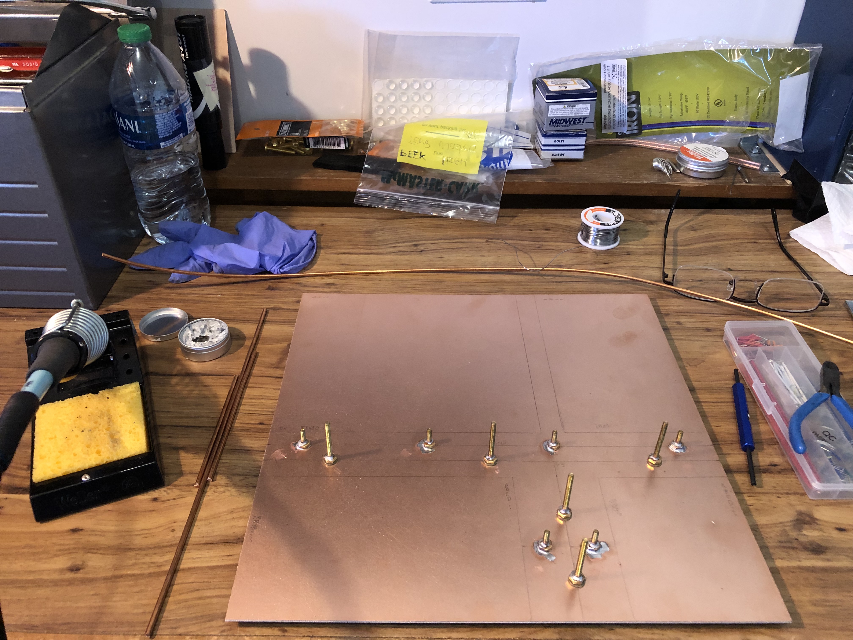
img/2023-06-20/IMG-1128.jpg
