gmofishsauce/yarc/img/2023-06-20/IMG-1131.jpg

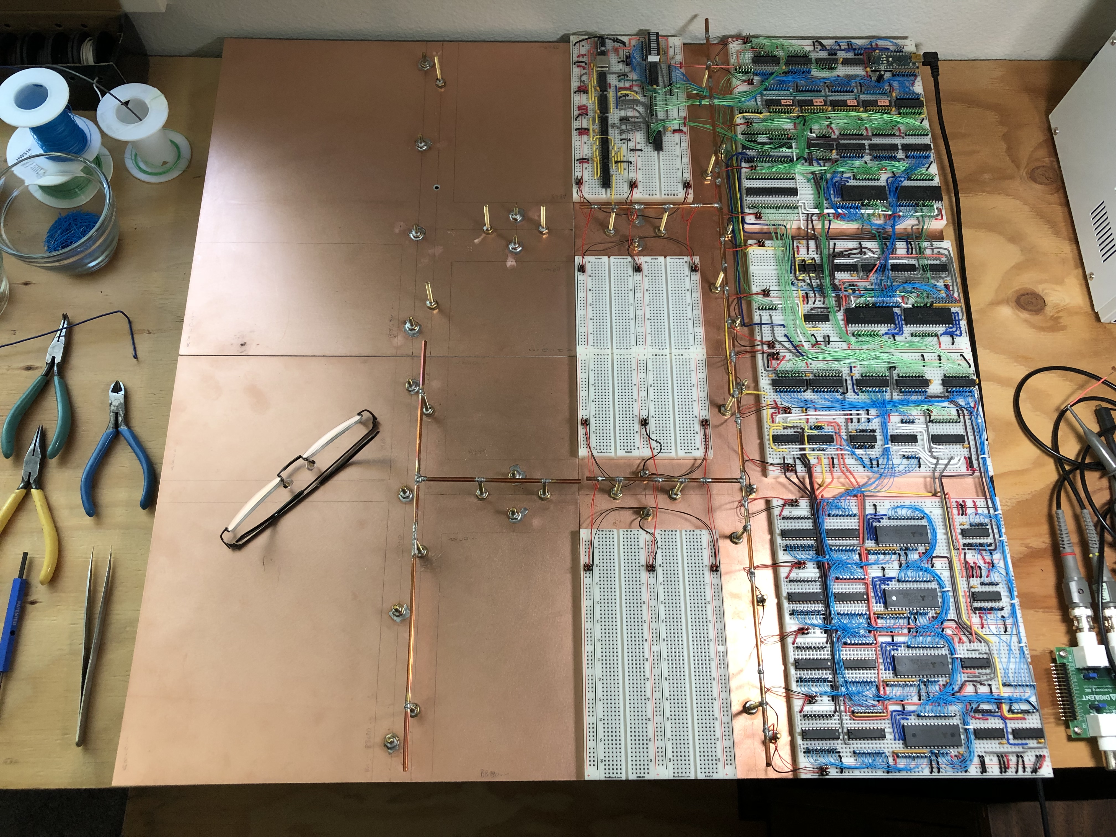
img/2023-06-20/IMG-1131.jpg
