gmofishsauce/yarc/img/2022-11-16/EarlyRegisterConstruction.jpeg

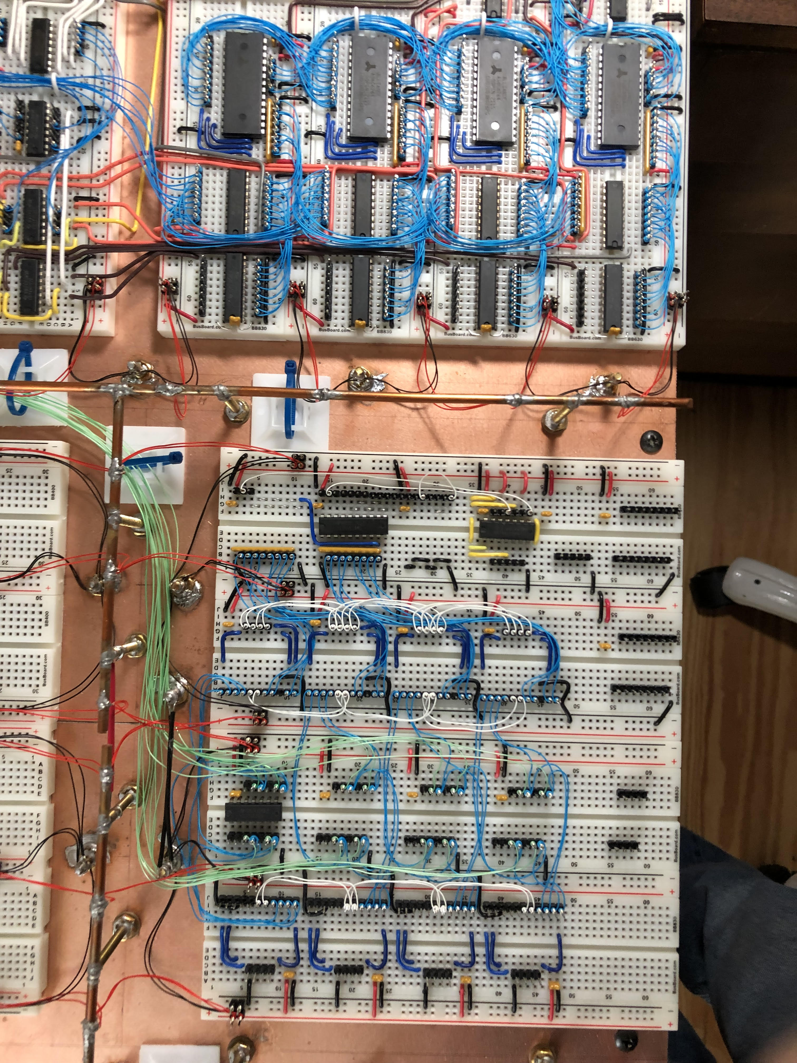
img/2022-11-16/EarlyRegisterConstruction.jpeg
