gmofishsauce/yarc/ard/yarc_fw/yarc_decls.h

// Copyright (c) Jeff Berkowitz 2021. All rights reserved.
//
// 456789012345678901234567890123456789012345678901234567890123456789012
//
// YARC-specific utility routines to read and write all YARC resources -
// instruction register IR, flags register F, microcode registers K0 through
// K3, general registers 0 through 3, microcode memory, ALU input and holding
// registers, and ALU memory.
//
void WriteIR(byte high, byte low);
void WriteK(byte k3, byte k2, byte k1, byte k0);
void WriteK(byte *k); // k3 at offset 0, k0 at offset 3
void ReadSlice(byte opcode, byte slice, byte *data, byte n);
int WriteSlice(byte opcode, byte slice, byte *data, byte n, bool panicOnFail);
void WriteMicrocode(byte opcode, byte *data, byte nWords);
void WriteMem16(unsigned short addr, unsigned short *data, short nWords);
void ReadMem16(unsigned short addr, unsigned short *data, short nWords);
void WriteMem8(unsigned short addr, unsigned char *data, short nBytes);
void ReadMem8(unsigned short addr, unsigned char *data, short nBytes);
byte WrMemFast(unsigned short addr, byte data);
byte RdMemFast(unsigned short addr);
void WriteReg(unsigned char reg, unsigned short value);
unsigned short ReadReg(unsigned char dataReg, unsigned short memAddr);
void WriteFlags(unsigned char flags);
byte ReadFlags();
void WriteALU(unsigned short offset, byte *data, unsigned short n);
void ReadALU(unsigned short offset, byte *data, unsigned short n, byte reg);
void WriteCheckALU(unsigned short offset, byte *data, unsigned short n);
