gmofishsauce/yarc/img/2023-06-20/IMG-0671.jpg

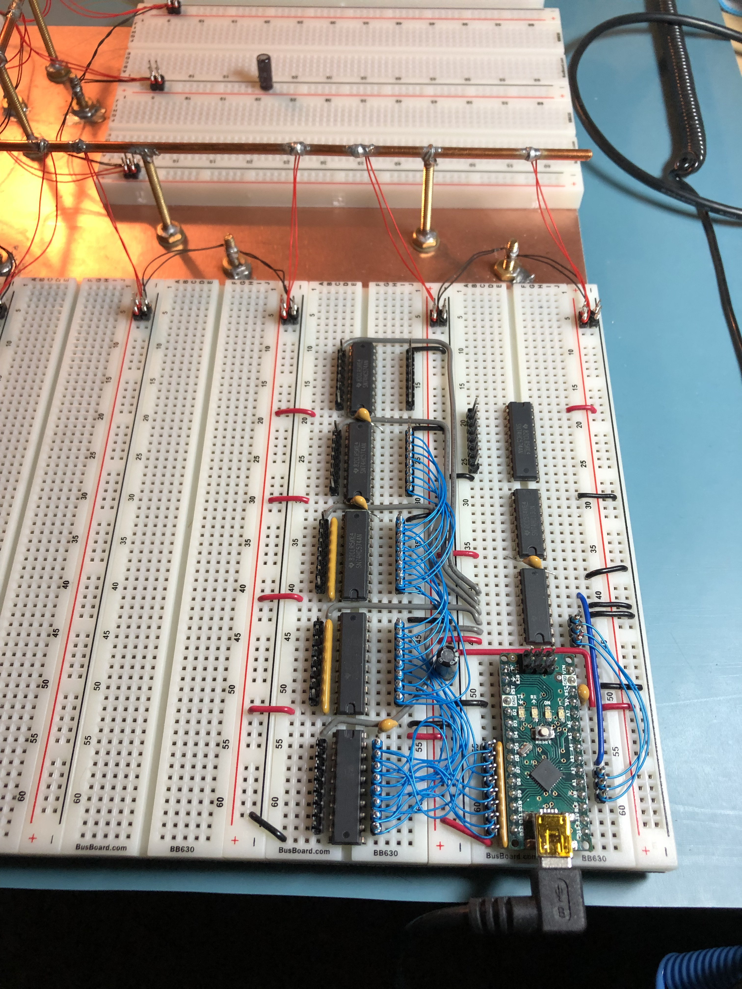
img/2023-06-20/IMG-0671.jpg
