gmofishsauce/yarc/img/2023-06-20/IMG-0962.jpg

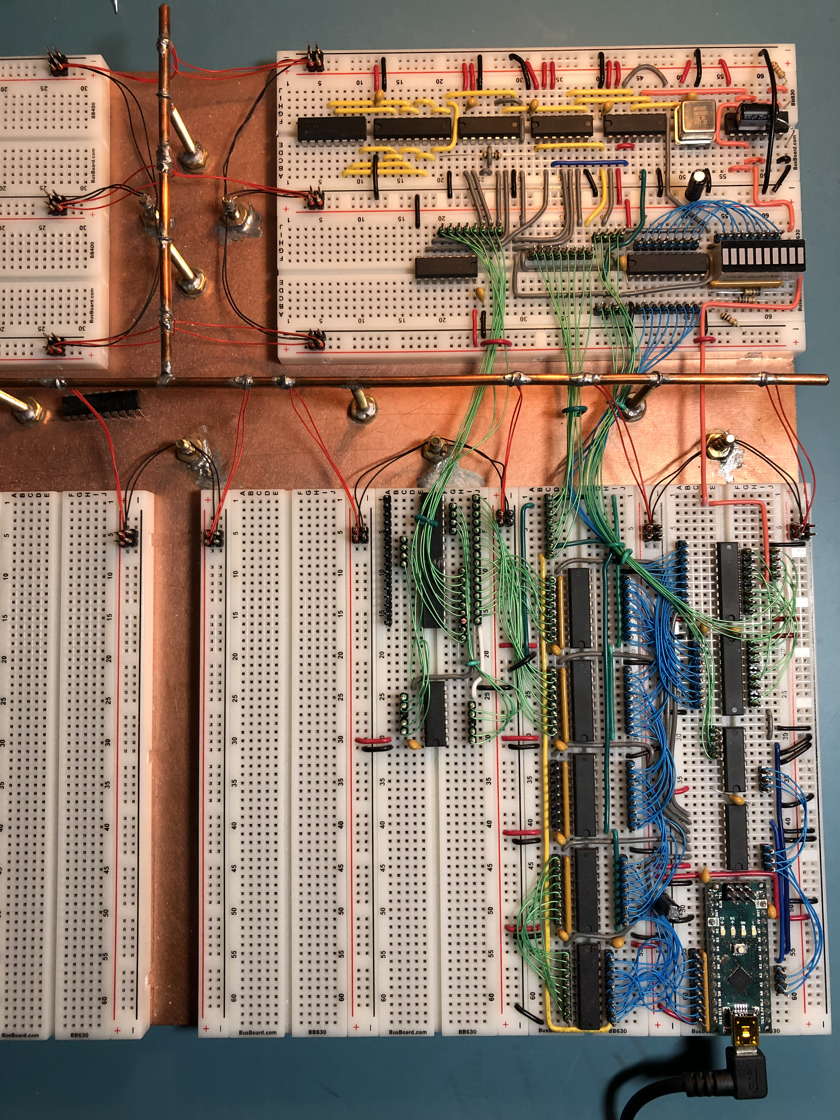
img/2023-06-20/IMG-0962.jpg
